vizicist/spacepalettepro/cad/SPP_hinge.3mf

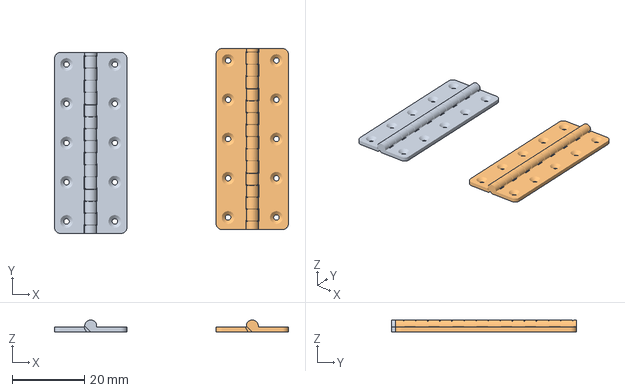
[picture p66: CAD file, 2025-05-30]
cad/SPP_hinge.3mf
64.6 x 51.1 x 3.33 mm
Print in place hinge FDM (x60y150).stl x 2
