vizicist/spacepalettepro/dxf/SPP_basebox_frontback.dxf

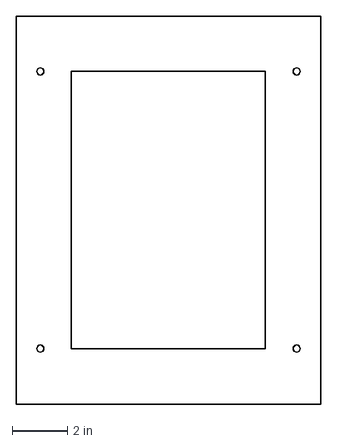
[picture p67: CAD file, 2022-07-03]
dxf/SPP_basebox_frontback.dxf
11.0 x 14.0 in
