vizicist/spacepalettepro/pre2025/dxf/SPP_baseboxes_medium_back_outer.dxf

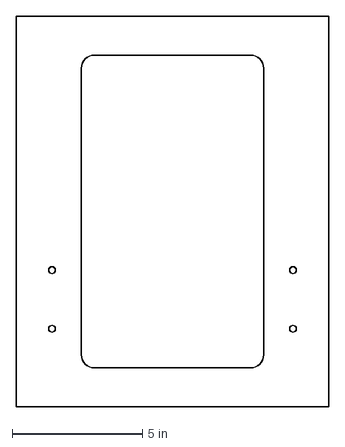
[picture p68: CAD file, 2022-09-05]
pre2025/dxf/SPP_baseboxes_medium_back_outer.dxf
12.0 x 15.0 in
