vizicist/spacepalettepro/pre2025/stl/AI3MX_amp_bracket_half.3mf

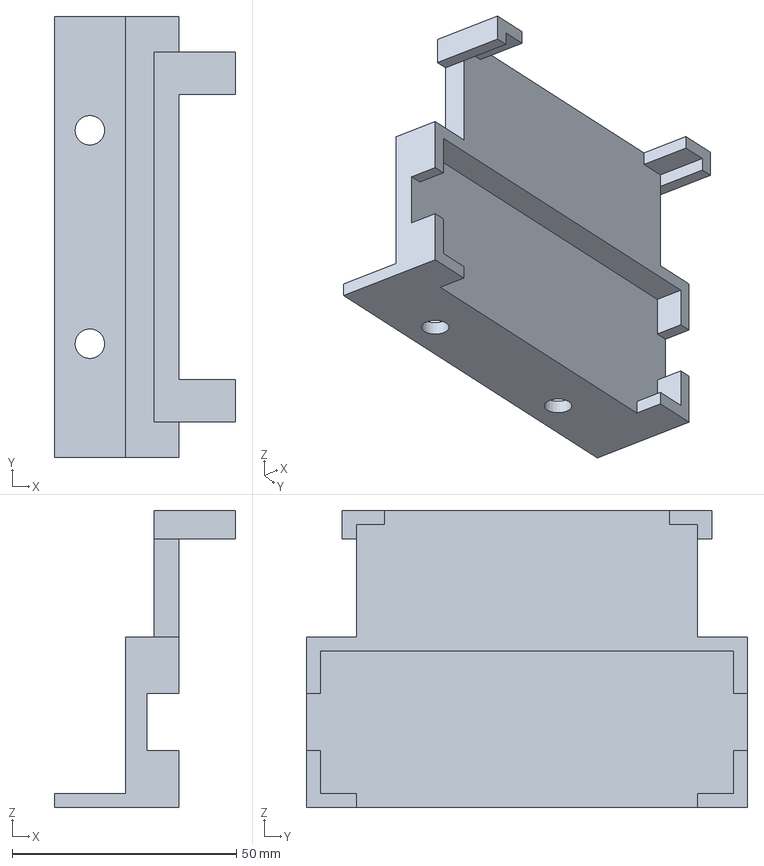
[picture p69: CAD file, 2021-08-21]
pre2025/stl/AI3MX_amp_bracket_half.3mf
40.5 x 98.4 x 66.3 mm
