vizicist/spacepalettepro/cad/SPP_angle.stl

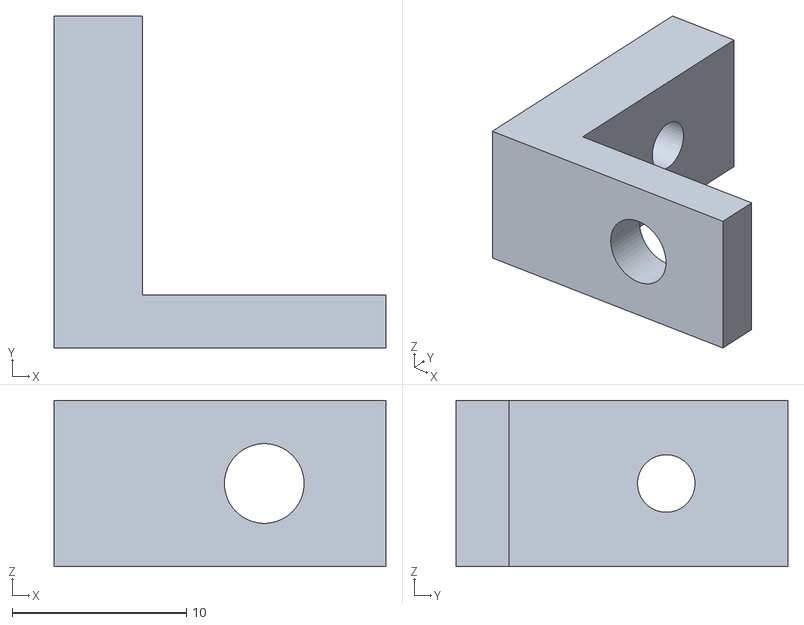
[picture p70: CAD file, 2025-05-30]
cad/SPP_angle.stl
19.0 x 19.0 x 9.53
