vizicist/spacepalettepro/pre2025/dxf/SPP_baseboxes_medium_back.dxf

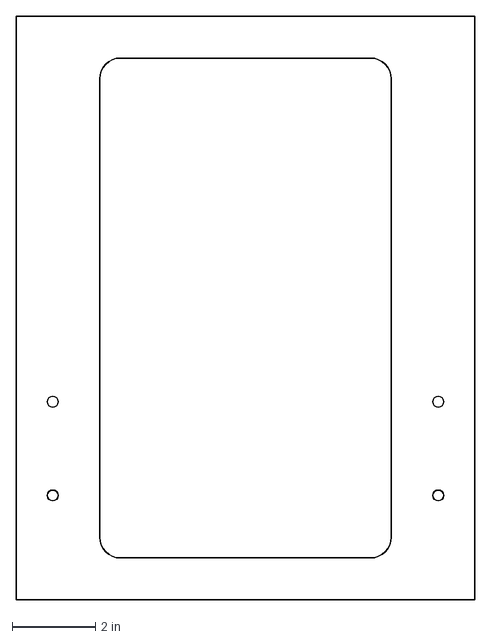
[picture p71: CAD file, 2022-09-05]
pre2025/dxf/SPP_baseboxes_medium_back.dxf
11.0 x 14.0 in
