vizicist/spacepalettepro/pre2025/stl/amp_bracket_half.stl

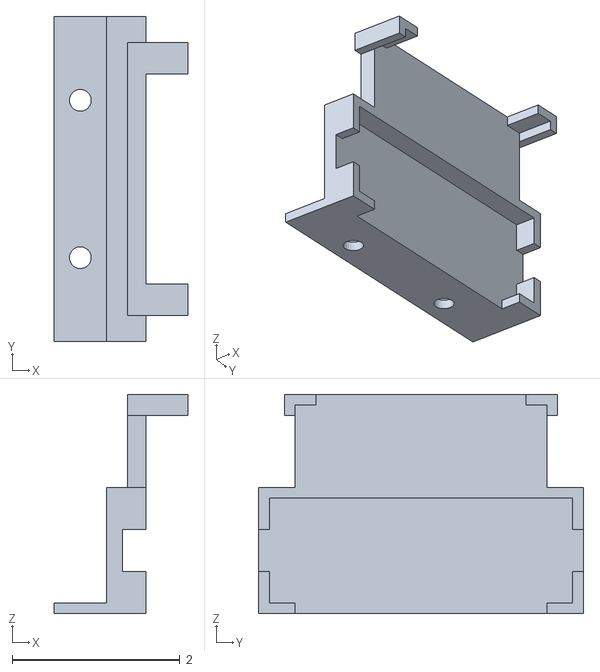
[picture p72: CAD file, 2021-08-21]
pre2025/stl/amp_bracket_half.stl
1.59 x 3.88 x 2.61
