vizicist/spacepalettepro/cad/SPP_ladder.3mf

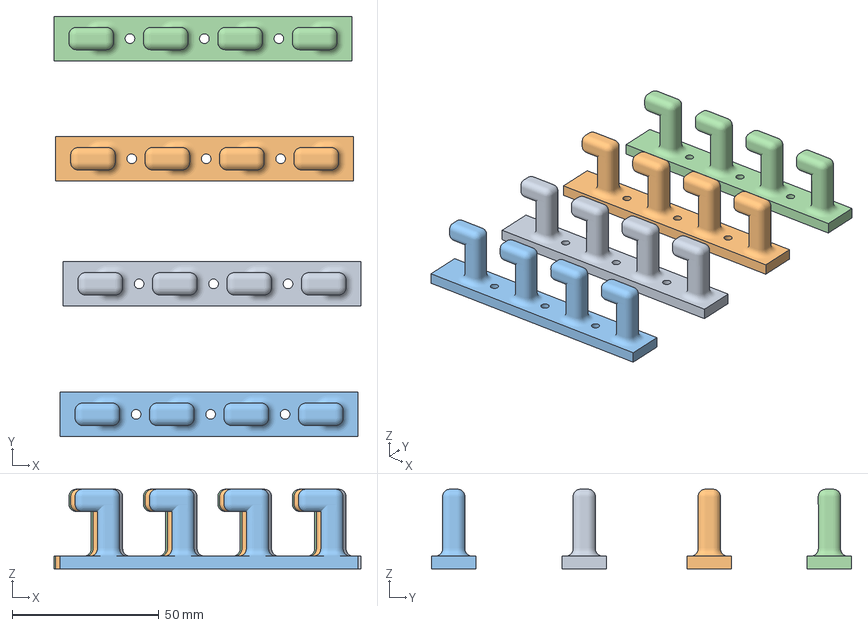
[picture p73: CAD file, 2025-05-30]
cad/SPP_ladder.3mf
104.7 x 143.4 x 27.2 mm
SPP_ladder.stl x 4
