vizicist/spacepalettepro/dxf/SPP_BaseHeadphones.dxf

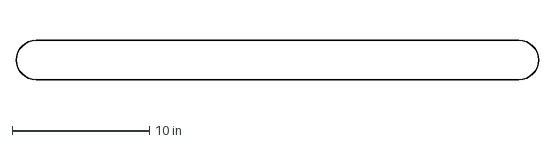
[picture p74: CAD file, 2021-08-06]
dxf/SPP_BaseHeadphones.dxf
38.0 x 2.88 in
