vizicist/spacepalettepro/pre2025/dxf/SPP_Layer7_back.dxf

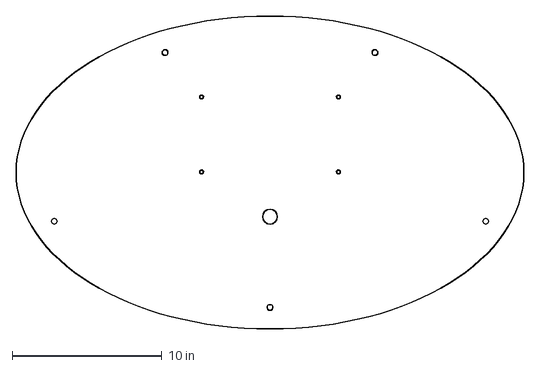
[picture p75: CAD file, 2022-08-22]
pre2025/dxf/SPP_Layer7_back.dxf
33.9 x 20.9 in
