vizicist/spacepalettepro/cad/SPP_sidesupport8.stl

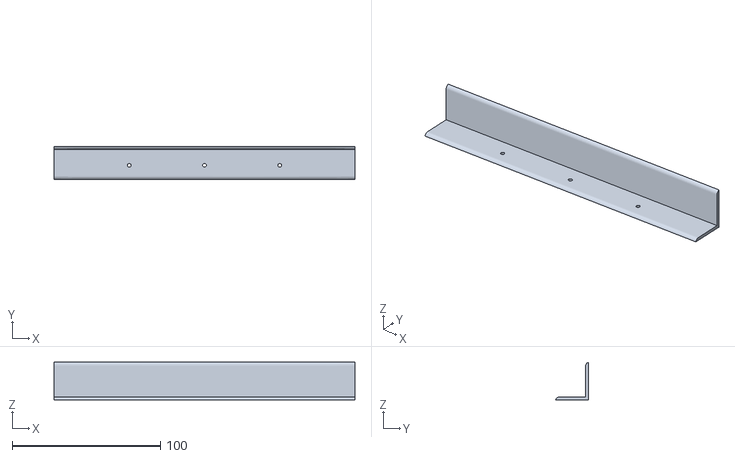
[picture p76: CAD file, 2025-05-30]
cad/SPP_sidesupport8.stl
203.2 x 22.2 x 25.4
