vizicist/spacepalettepro/pre2025/dxf/SPP_baseboxes_small_side.dxf

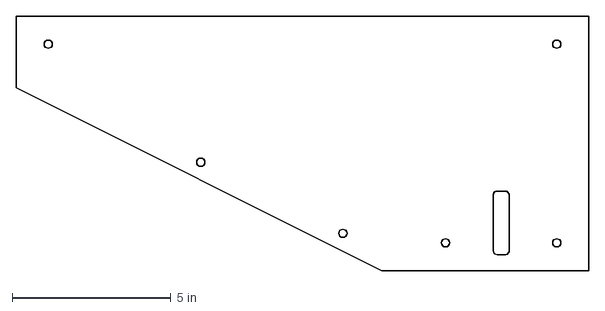
[picture p77: CAD file, 2022-08-22]
pre2025/dxf/SPP_baseboxes_small_side.dxf
18.0 x 8.00 in
