vizicist/spacepalettepro/pre2025/stl/amp_bracket.obj

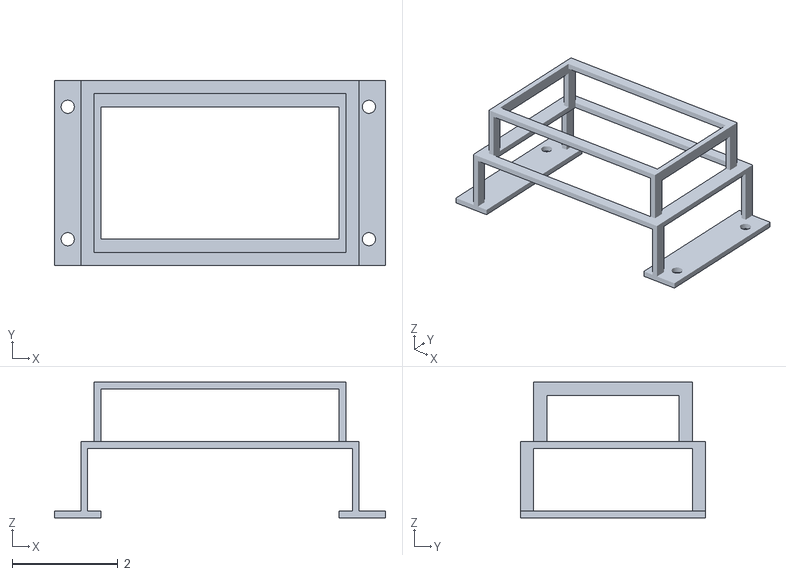
[picture p78: CAD file, 2021-08-17]
pre2025/stl/amp_bracket.obj
6.25 x 3.50 x 2.56
