vizicist/spacepalettepro/cad/SPP_ladder_4.3mf

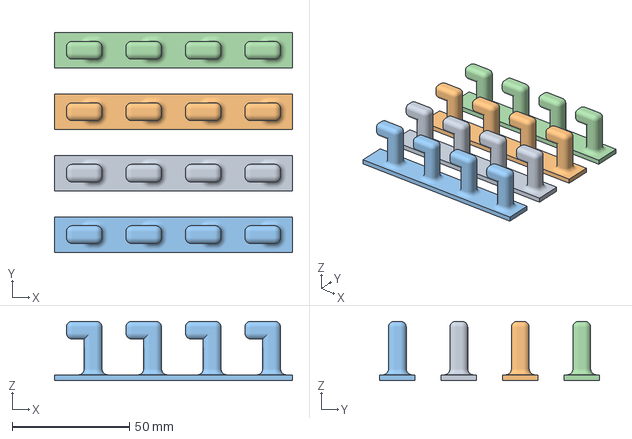
[picture p79: CAD file, 2025-05-30]
cad/SPP_ladder_4.3mf
101.6 x 94.0 x 25.4 mm
SPP_ladder.stl x 4
