vizicist/spacepalettepro/pre2025/dxf/SPP_baseboxes_small_back.dxf

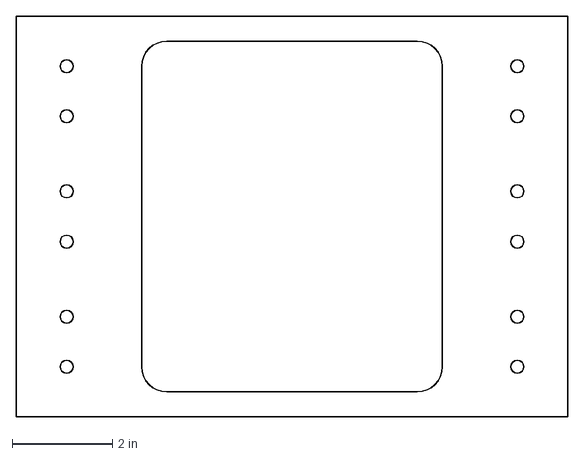
[picture p80: CAD file, 2022-08-15]
pre2025/dxf/SPP_baseboxes_small_back.dxf
11.0 x 8.00 in
