vizicist/spacepalettepro/pre2025/stl/corner_mount.stl

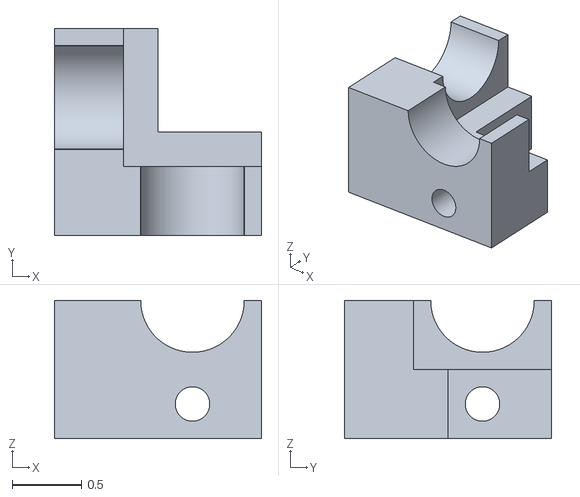
[picture p81: CAD file, 2021-08-06]
pre2025/stl/corner_mount.stl
1.50 x 1.50 x 1.00
