vizicist/spacepalettepro/cad/SPP_ladder_holes.3mf

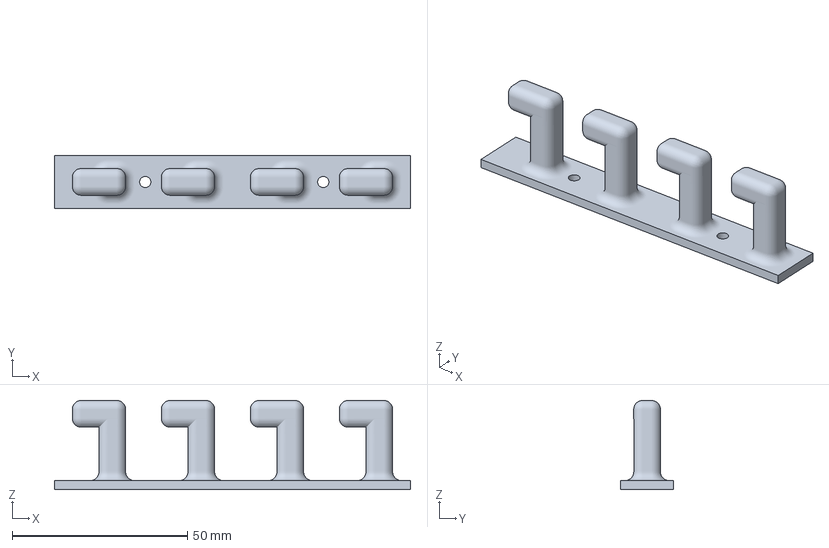
[picture p82: CAD file, 2025-05-30]
cad/SPP_ladder_holes.3mf
101.6 x 15.2 x 25.4 mm
