vizicist/spacepalettepro/pre2025/dxf/SPP_BaseBottom.dxf

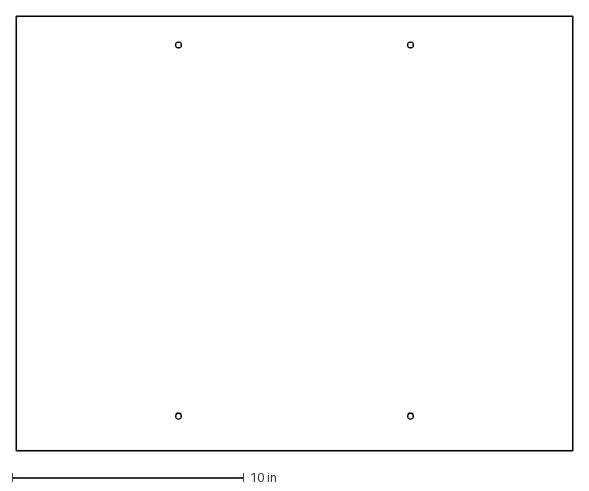
[picture p83: CAD file, 2022-08-15]
pre2025/dxf/SPP_BaseBottom.dxf
24.0 x 18.8 in
