vizicist/spacepalettepro/cad/SPP_portpanel_orig.3mf

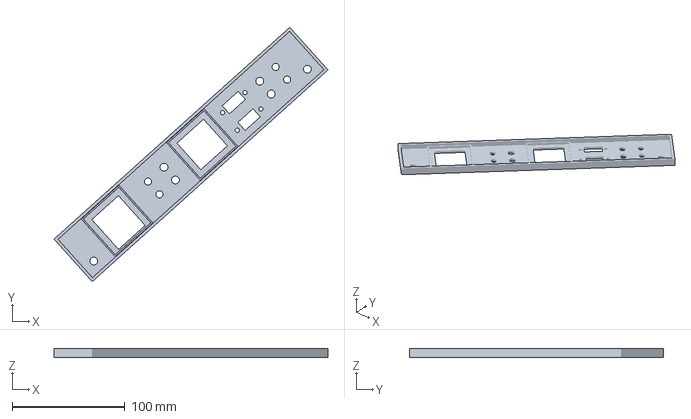
[picture p84: CAD file, 2025-05-30]
cad/SPP_portpanel_orig.3mf
243.3 x 225.8 x 7.62 mm
