vizicist/spacepalettepro/pre2025/dxf/SPP_BaseBottomLedge.dxf

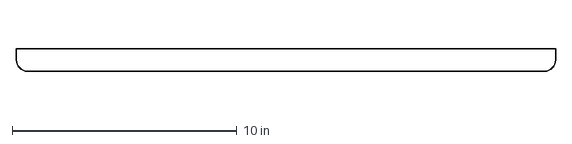
[picture p85: CAD file, 2022-08-15]
pre2025/dxf/SPP_BaseBottomLedge.dxf
24.0 x 1.00 in
