vizicist/spacepalettepro/cad/SPP_InnerEdge_B_0.25.stl

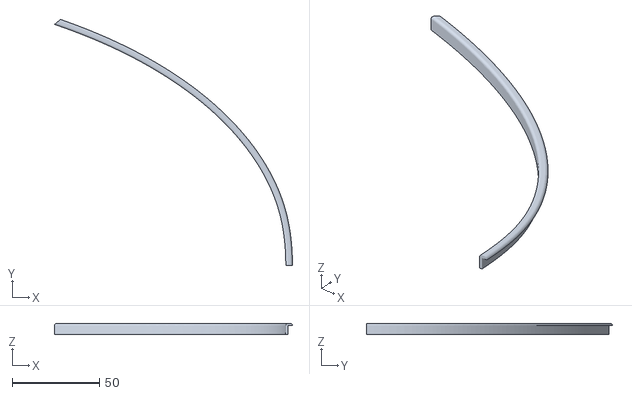
[picture p86: CAD file, 2025-05-30]
cad/SPP_InnerEdge_B_0.25.stl
136.2 x 140.9 x 6.35
