vizicist/spacepalettepro/pre2025/dxf/SPP_BaseSpeaker.dxf

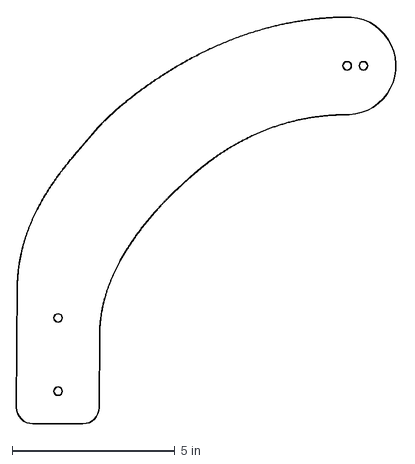
[picture p87: CAD file, 2022-07-30]
pre2025/dxf/SPP_BaseSpeaker.dxf
11.7 x 12.5 in
