vizicist/spacepalettepro/cad/SPP_Edge_All.3mf

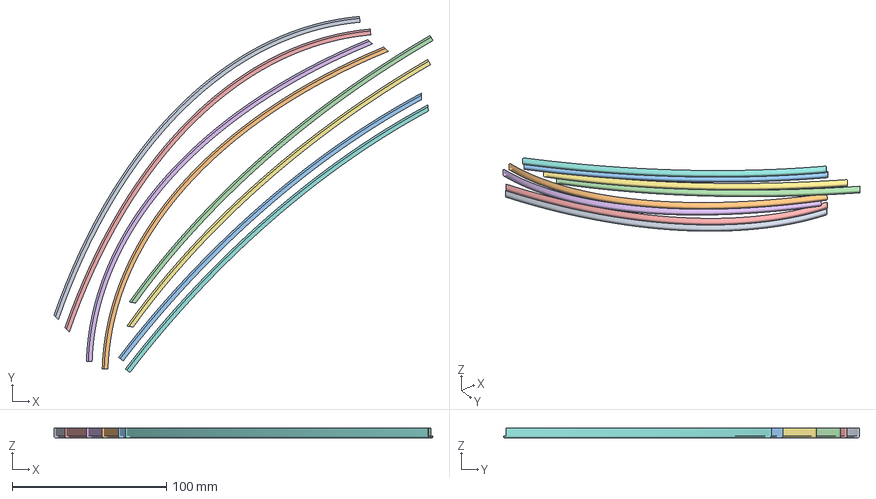
[picture p88: CAD file, 2025-05-30]
cad/SPP_Edge_All.3mf
246.1 x 231.2 x 6.35 mm
SPP_Edge_B_0.25.stl x 2
SPP_Edge_B_0.25_flipped.stl x 2
SPP_Edge_A_0.25.stl x 2
SPP_Edge_A_0.25_flipped.stl x 2
