vizicist/spacepalettepro/pre2025/dxf/SPP_BaseHeadphones_small.dxf

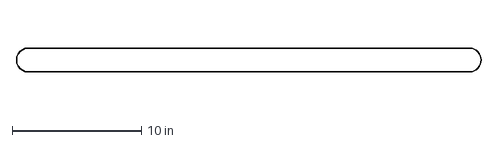
[picture p89: CAD file, 2022-07-30]
pre2025/dxf/SPP_BaseHeadphones_small.dxf
36.0 x 1.86 in
