vizicist/spacepalettepro/cad/SPP_hingetest.3mf

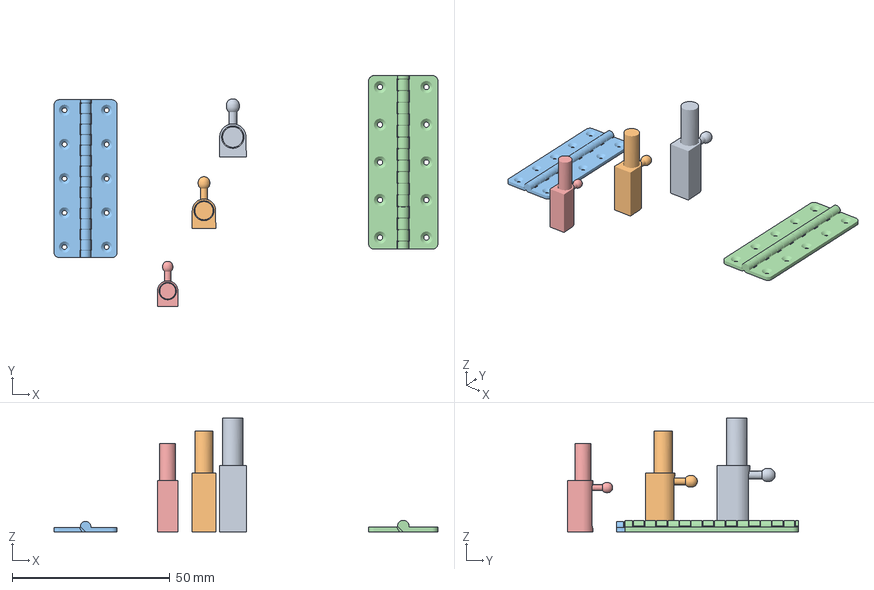
[picture p90: CAD file, 2025-05-30]
cad/SPP_hingetest.3mf
121.6 x 73.1 x 36.0 mm
SPP_slidercut.stl x 3
Print in place hinge FDM (x60y150).stl x 2
