vizicist/spacepalettepro/pre2025/dxf/SPP_BaseBack_insert.dxf

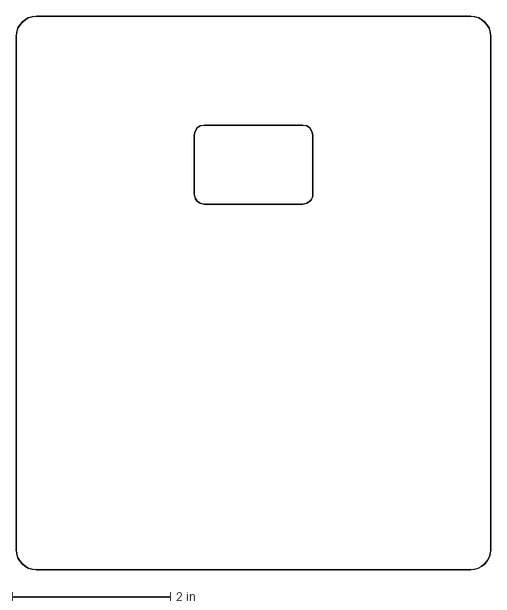
[picture p91: CAD file, 2022-07-30]
pre2025/dxf/SPP_BaseBack_insert.dxf
6.00 x 7.00 in
