vizicist/spacepalettepro/cad/SPP_headphonehook.3mf

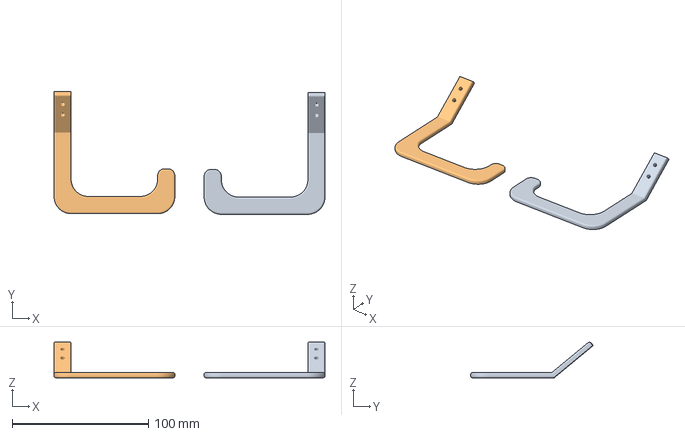
[picture p92: CAD file, 2025-05-30]
cad/SPP_headphonehook.3mf
199.0 x 90.1 x 26.1 mm
SPP_headphonehook.stl x 2
