vizicist/spacepalettepro/pre2025/dxf/SPP_baseboxes_large_back.dxf

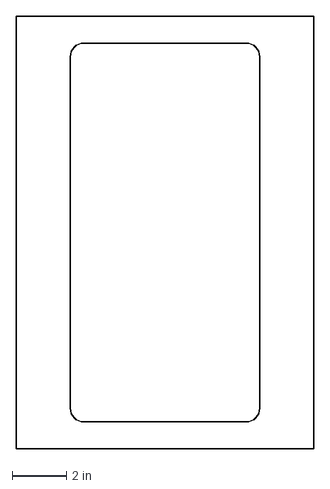
[picture p93: CAD file, 2022-07-30]
pre2025/dxf/SPP_baseboxes_large_back.dxf
11.0 x 16.0 in
