vizicist/spacepalettepro/cad/SPP_Edge_A_0.25.stl

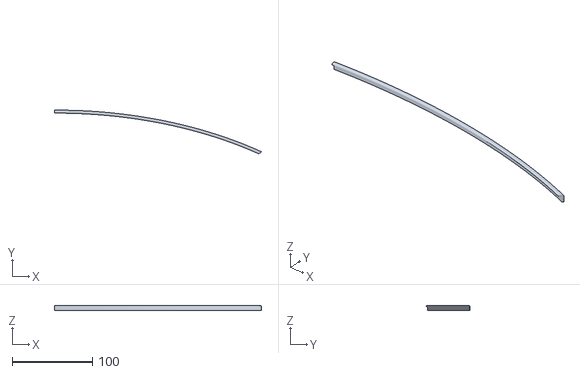
[picture p94: CAD file, 2025-05-30]
cad/SPP_Edge_A_0.25.stl
257.3 x 54.5 x 6.35
