vizicist/spacepalettepro/pre2025/dxf/SPP_baseboxes_small_top.dxf

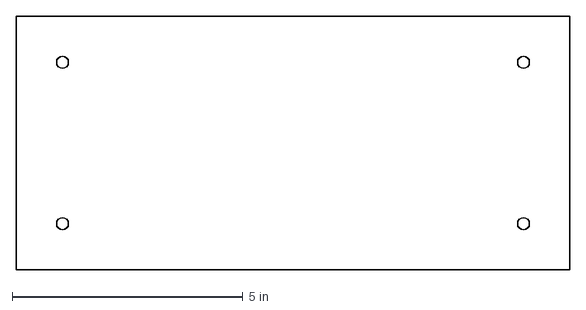
[picture p95: CAD file, 2022-07-30]
pre2025/dxf/SPP_baseboxes_small_top.dxf
12.0 x 5.50 in
