vizicist/spacepalettepro/cad/SPP_pinpanel.stl

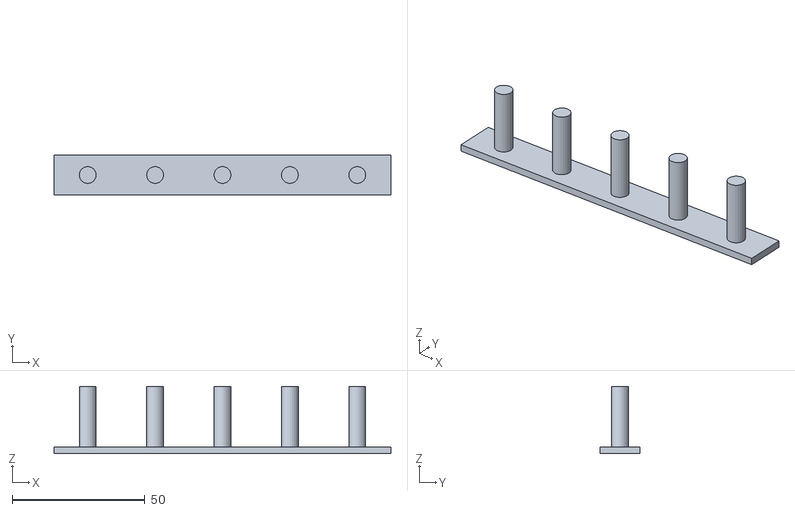
[picture p96: CAD file, 2025-05-30]
cad/SPP_pinpanel.stl
127.0 x 15.2 x 25.4
