vizicist/spacepalettepro/pre2025/dxf/SPP_BaseBack.dxf

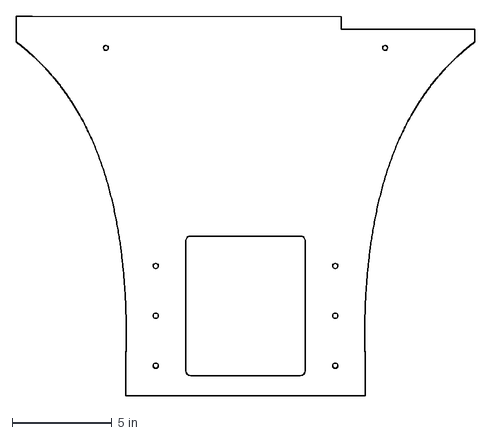
[picture p97: CAD file, 2022-07-30]
pre2025/dxf/SPP_BaseBack.dxf
23.0 x 19.0 in
