vizicist/spacepalettepro/cad/SPP_back.dxf

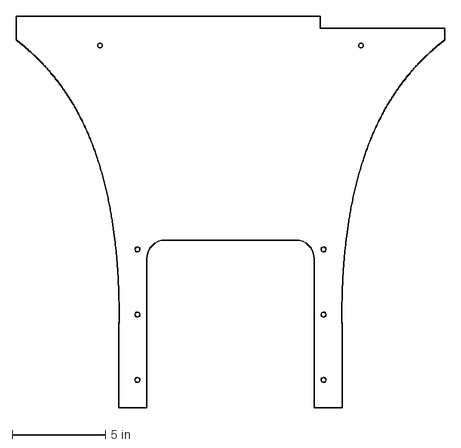
[picture p98: CAD file, 2025-05-30]
cad/SPP_back.dxf
23.0 x 21.0 in
