vizicist/spacepalettepro/pre2025/dxf/SPP_baseboxes_medium_side.dxf

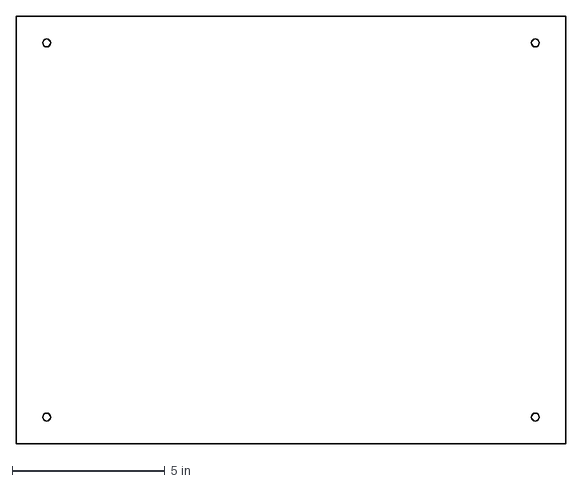
[picture p99: CAD file, 2022-07-30]
pre2025/dxf/SPP_baseboxes_medium_side.dxf
18.0 x 14.0 in
