vizicist/spacepalettepro/cad/SPP_headphonehookold.3mf

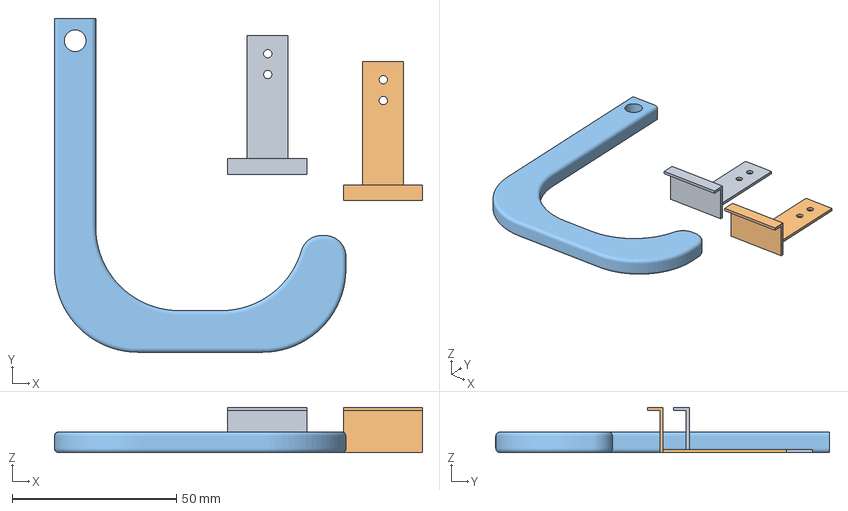
[picture p100: CAD file, 2025-05-30]
cad/SPP_headphonehookold.3mf
112.1 x 101.6 x 13.8 mm
SPP_latch.stl x 2
SPP_headphonehook.stl
