vizicist/spacepalettepro/pre2025/dxf/SPP_baseboxes_large_side.dxf

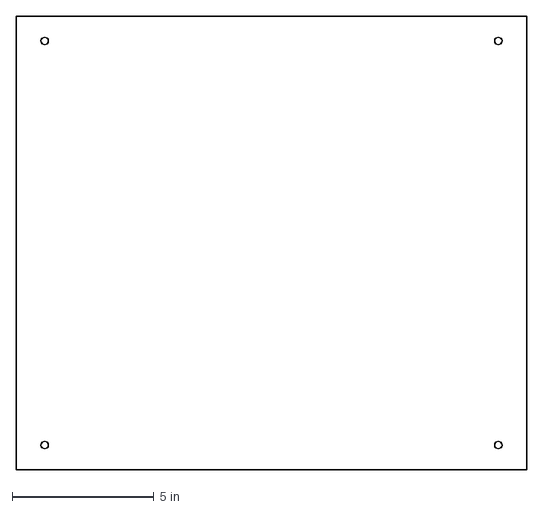
[picture p101: CAD file, 2022-07-14]
pre2025/dxf/SPP_baseboxes_large_side.dxf
18.0 x 16.0 in
