vizicist/spacepalettepro/cad/SPP_slider.3mf

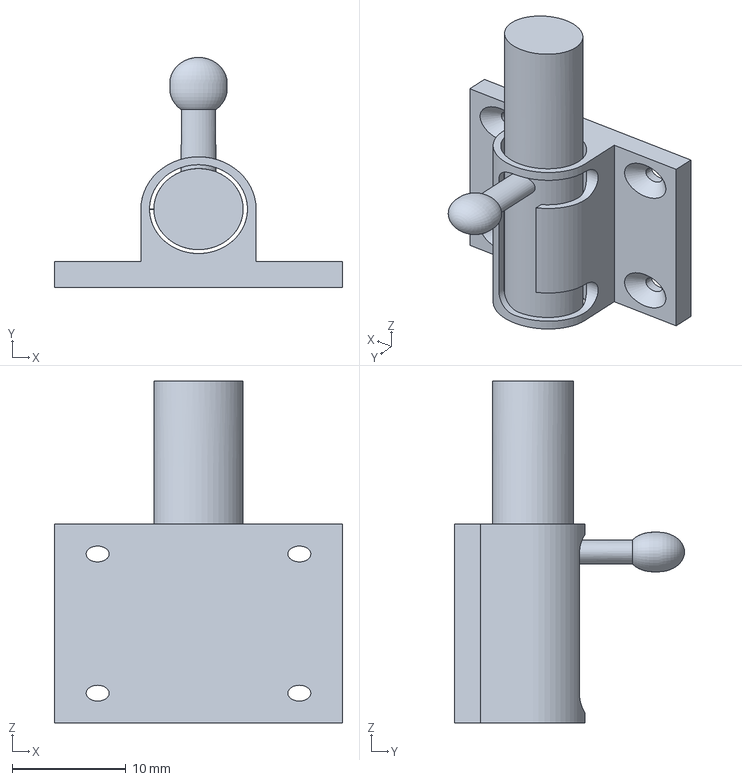
[picture p102: CAD file, 2025-05-30]
cad/SPP_slider.3mf
25.3 x 20.2 x 30.0 mm
