vizicist/spacepalettepro/pre2025/dxf/SPP_BaseFront.dxf

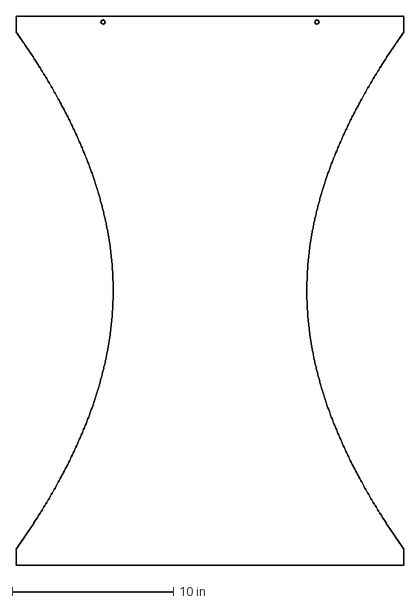
[picture p103: CAD file, 2022-01-15]
pre2025/dxf/SPP_BaseFront.dxf
24.0 x 34.0 in
