vizicist/spacepalettepro/cad/SPP_channels_hooks.3mf

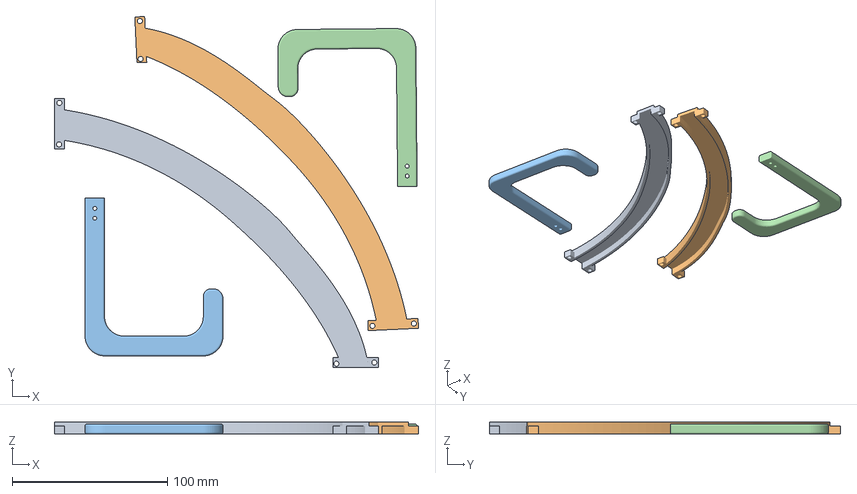
[picture p104: CAD file, 2025-05-30]
cad/SPP_channels_hooks.3mf
234.1 x 225.8 x 7.62 mm
SPP_wirechannel.stl_1
SPP_wirechannel.stl_2
SPP_headphonehook.stl x 2
