vizicist/spacepalettepro/pre2025/dxf/SPP_MonLayer5.dxf

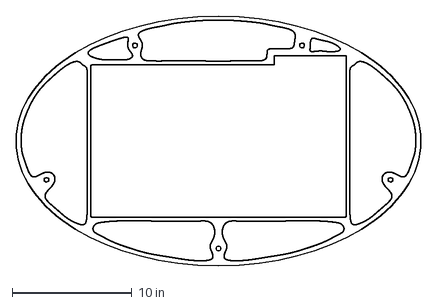
[picture p105: CAD file, 2022-01-15]
pre2025/dxf/SPP_MonLayer5.dxf
33.9 x 20.9 in
