vizicist/spacepalettepro/cad/SPP_test.stl

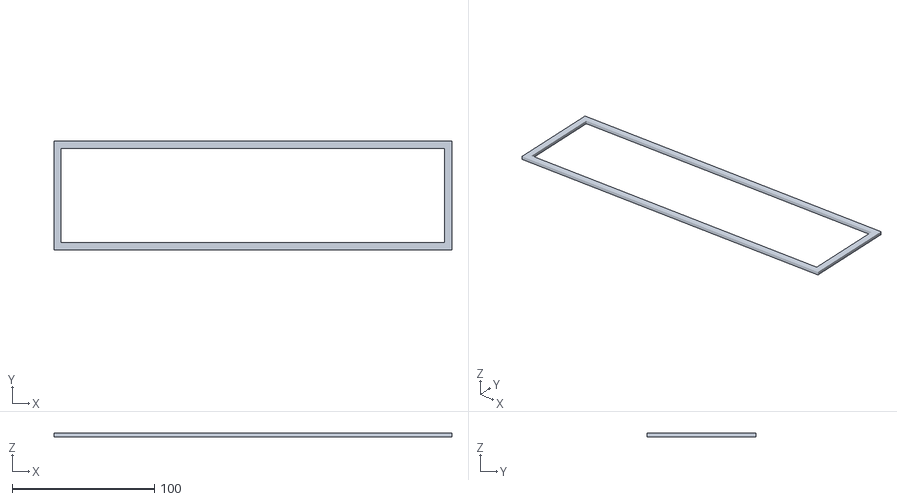
[picture p106: CAD file, 2025-05-30]
cad/SPP_test.stl
279.4 x 76.2 x 2.54
