vizicist/spacepalettepro/pre2025/dxf/SPP_MonLayer6_back.dxf

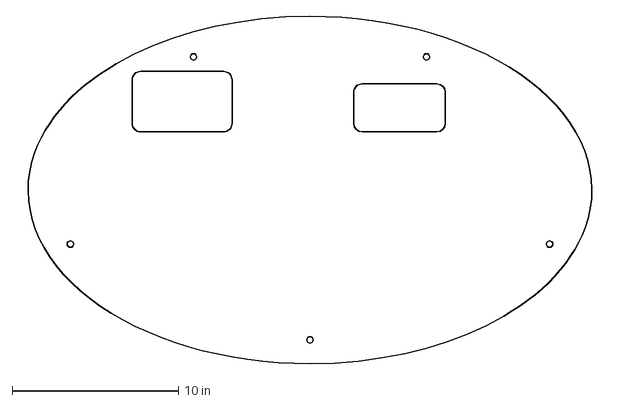
[picture p107: CAD file, 2022-01-15]
pre2025/dxf/SPP_MonLayer6_back.dxf
35.3 x 20.9 in
