vizicist/spacepalettepro/cad/SPP_fanpanel.dxf

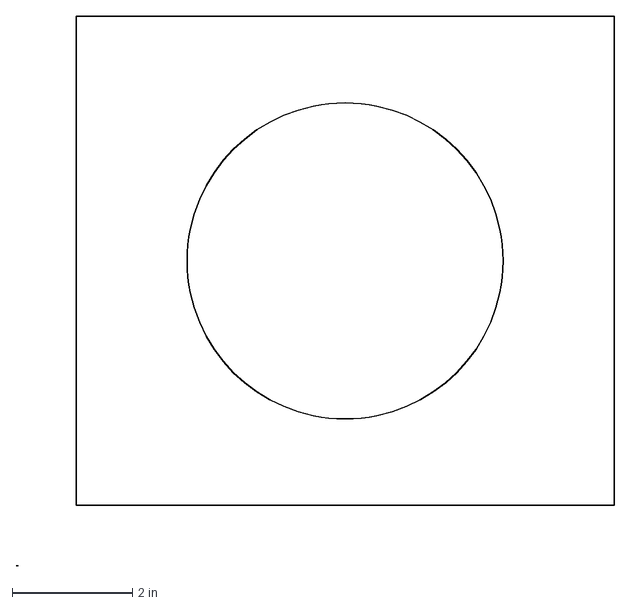
[picture p108: CAD file, 2025-05-30]
cad/SPP_fanpanel.dxf
9.94 x 9.13 in
