vizicist/spacepalettepro/pre2025/dxf/SPP_BaseBackBottom.dxf

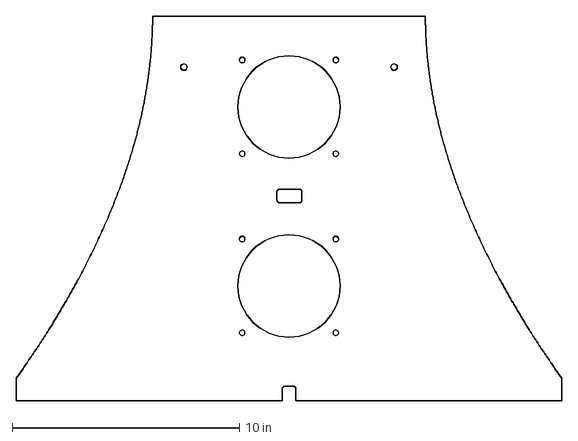
[picture p109: CAD file, 2021-08-20]
pre2025/dxf/SPP_BaseBackBottom.dxf
24.0 x 16.9 in
