vizicist/spacepalettepro/cad/SPP_mon_key_platform.3mf

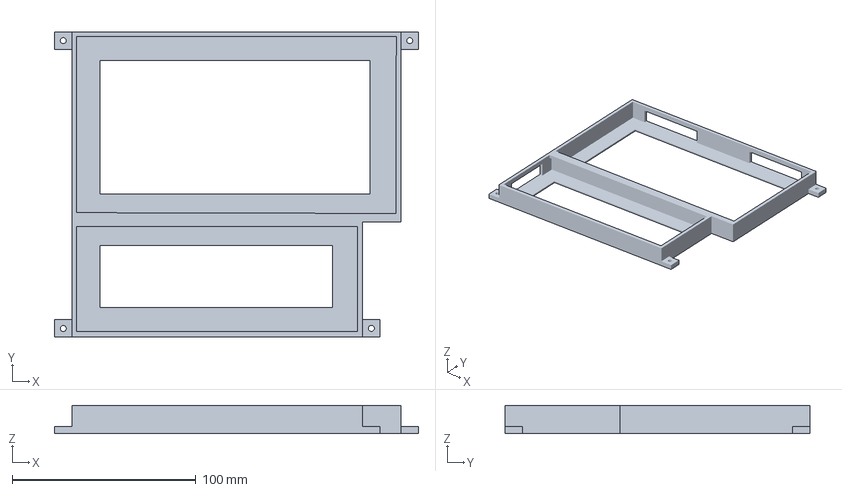
[picture p110: CAD file, 2025-05-30]
cad/SPP_mon_key_platform.3mf
197.9 x 166.0 x 15.2 mm
