vizicist/spacepalettepro/pre2025/dxf/SPP_MonLayer1_face.dxf

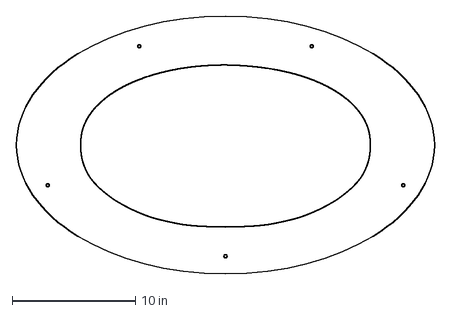
[picture p111: CAD file, 2021-08-10]
pre2025/dxf/SPP_MonLayer1_face.dxf
33.9 x 20.9 in
