vizicist/spacepalettepro/pre2025/dxf/SPP_BaseKeyboard.dxf

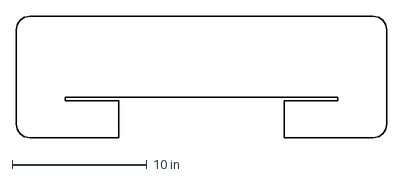
[picture p112: CAD file, 2021-08-06]
pre2025/dxf/SPP_BaseKeyboard.dxf
27.5 x 9.00 in
