vizicist/spacepalettepro/cad/SPP_back_insert.dxf

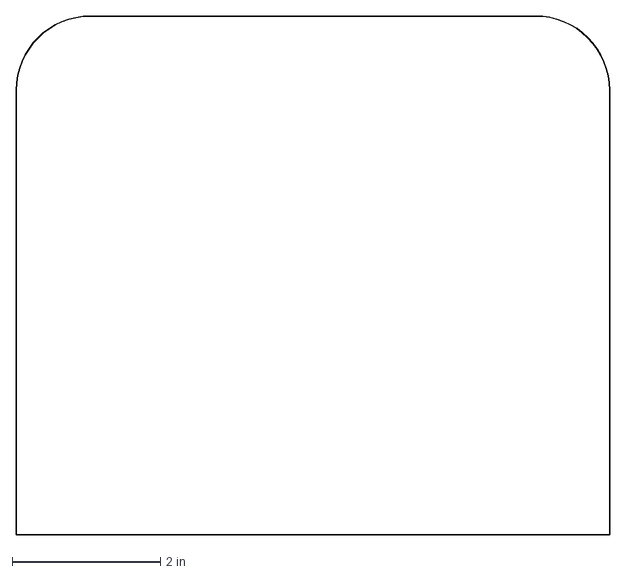
[picture p113: CAD file, 2025-05-30]
cad/SPP_back_insert.dxf
8.00 x 7.00 in
