vizicist/spacepalettepro/pre2025/dxf/SPP_Layer2.dxf

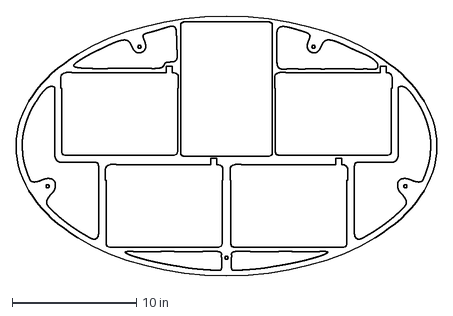
[picture p114: CAD file, 2021-08-06]
pre2025/dxf/SPP_Layer2.dxf
33.9 x 20.9 in
