vizicist/spacepalettepro/cad/SPP_Edge_A_all.3mf

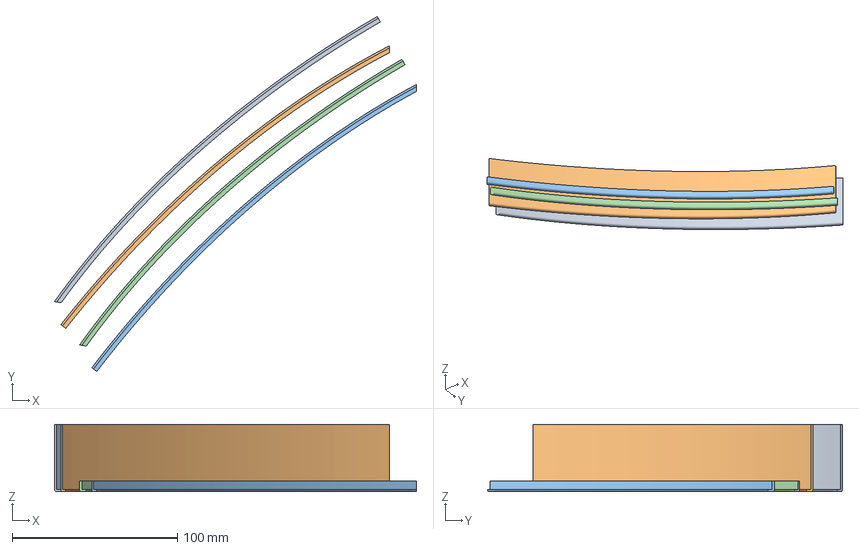
[picture p115: CAD file, 2025-05-30]
cad/SPP_Edge_A_all.3mf
219.4 x 215.1 x 40.8 mm
SPP_Edge_A_1.5_flipped.stl
SPP_Edge_A_1.5.stl
SPP_Edge_A_0.25.stl
SPP_Edge_A_0.25_flipped.stl
