vizicist/spacepalettepro/cad/SPP_pinangled.stl

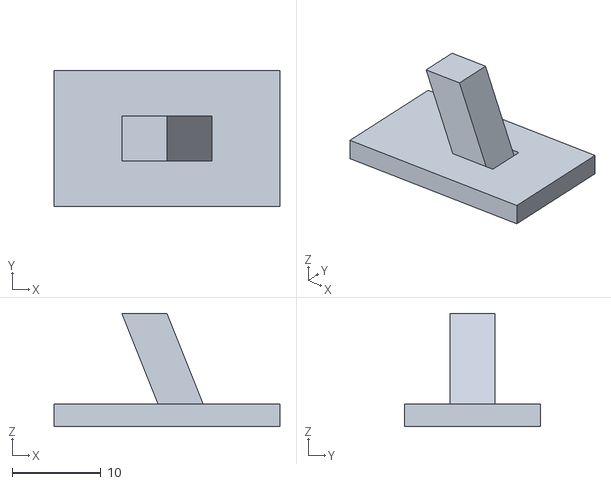
[picture p117: CAD file, 2025-05-30]
cad/SPP_pinangled.stl
25.4 x 15.2 x 12.7
