vizicist/spacepalettepro/pre2025/dxf/SPP_MonLayer2_3_bottom.dxf

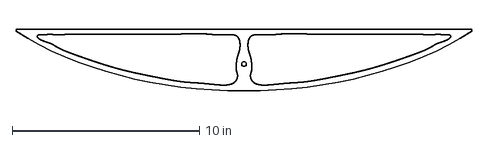
[picture p118: CAD file, 2021-08-06]
pre2025/dxf/SPP_MonLayer2_3_bottom.dxf
24.4 x 3.31 in
