vizicist/spacepalettepro/cad/SPP_switchcover.stl

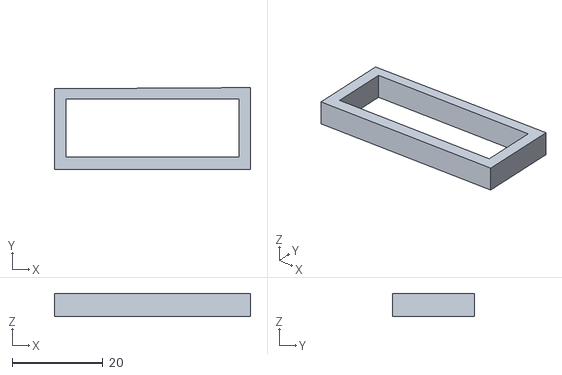
[picture p119: CAD file, 2025-05-30]
cad/SPP_switchcover.stl
43.2 x 18.0 x 5.08
