vizicist/spacepalettepro/pre2025/dxf/SPP_MonLayer4.dxf

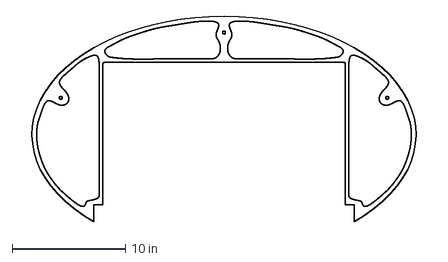
[picture p120: CAD file, 2021-08-06]
pre2025/dxf/SPP_MonLayer4.dxf
36.6 x 18.1 in
