vizicist/spacepalettepro/cad/SPP_basefrontb.dxf

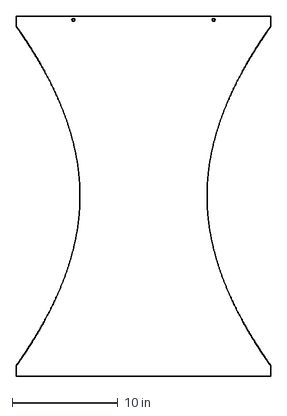
[picture p121: CAD file, 2025-05-30]
cad/SPP_basefrontb.dxf
24.0 x 34.0 in
