vizicist/spacepalettepro/pre2025/dxf/SPP_Layer3.dxf

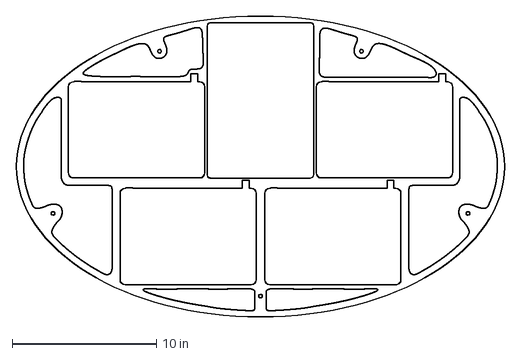
[picture p122: CAD file, 2021-08-06]
pre2025/dxf/SPP_Layer3.dxf
33.9 x 20.9 in
