vizicist/spacepalettepro/cad/SPP_Speaker.dxf

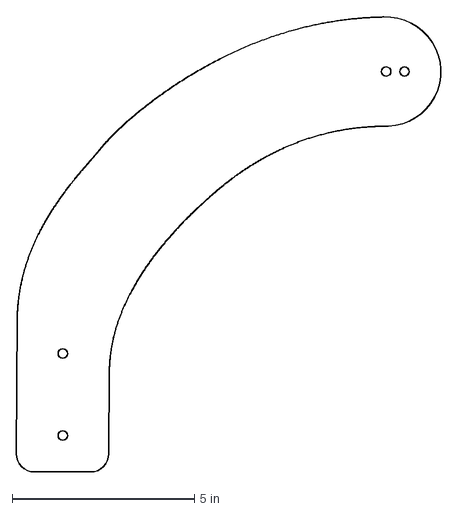
[picture p123: CAD file, 2025-05-30]
cad/SPP_Speaker.dxf
11.7 x 12.5 in
