vizicist/spacepalettepro/pre2025/dxf/SPP_MonLayer2_3_leftright.dxf

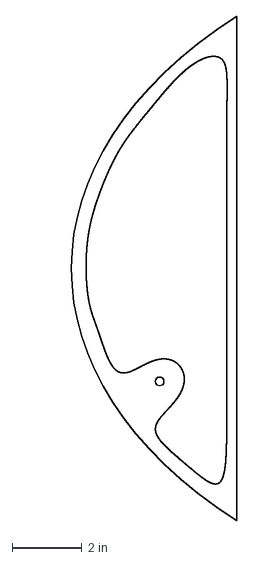
[picture p124: CAD file, 2021-08-06]
pre2025/dxf/SPP_MonLayer2_3_leftright.dxf
6.34 x 14.5 in
