vizicist/spacepalettepro/cad/SPP_wirechannel.stl

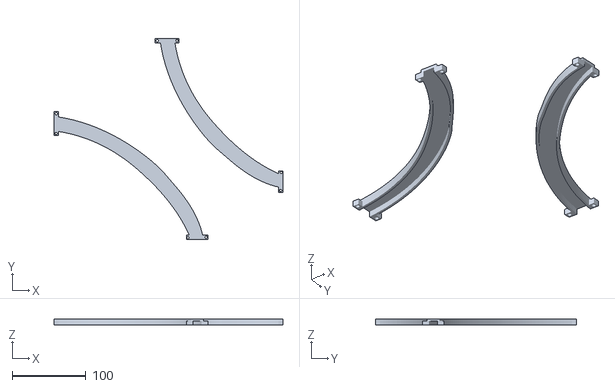
[picture p125: CAD file, 2025-05-30]
cad/SPP_wirechannel.stl
309.8 x 272.0 x 7.62
