vizicist/spacepalettepro/cad/SPP_nuc_support.3mf

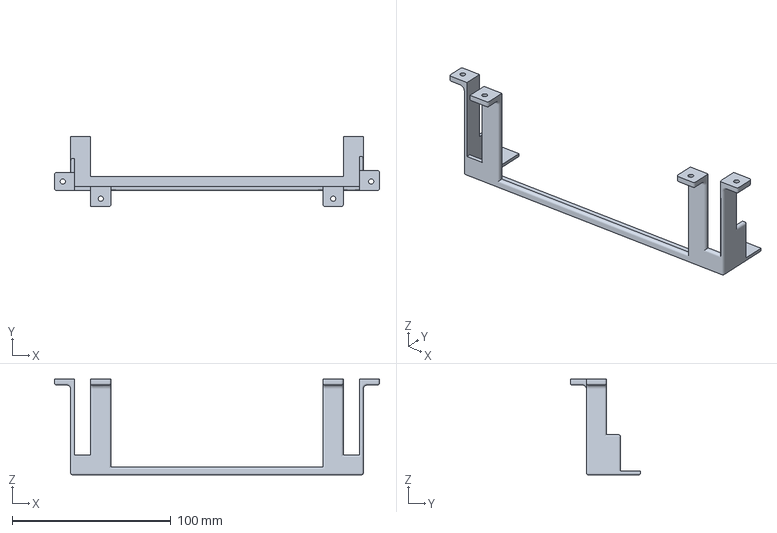
[picture p127: CAD file, 2025-05-30]
cad/SPP_nuc_support.3mf
205.0 x 44.4 x 60.5 mm
