vizicist/spacepalettepro/cad/SPP_latch.3mf

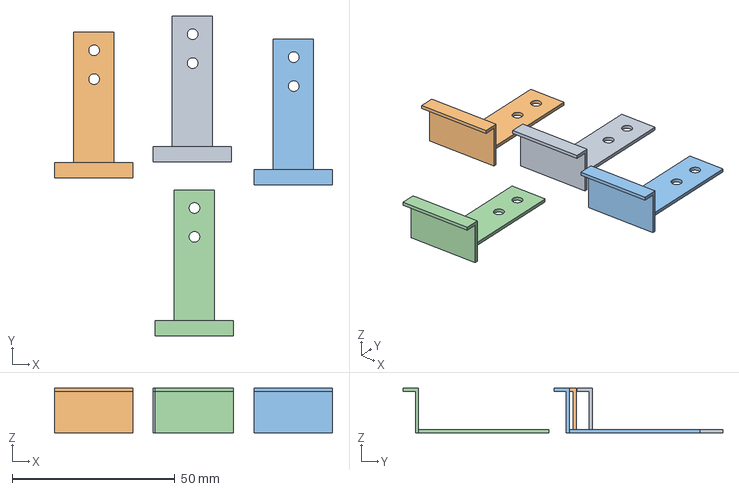
[picture p129: CAD file, 2025-05-30]
cad/SPP_latch.3mf
85.5 x 98.4 x 13.8 mm
SPP_latch.stl x 4
