vizicist/spacepalettepro/pre2025/dxf/SPP_MonLayer1orig_face.dxf

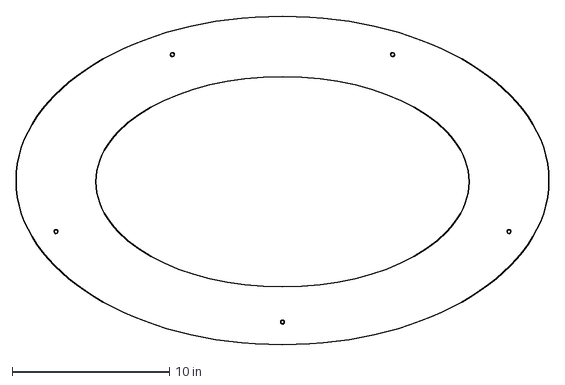
[picture p130: CAD file, 2021-08-06]
pre2025/dxf/SPP_MonLayer1orig_face.dxf
33.9 x 20.9 in
