vizicist/spacepalettepro/cad/SPP_usbholder.3mf

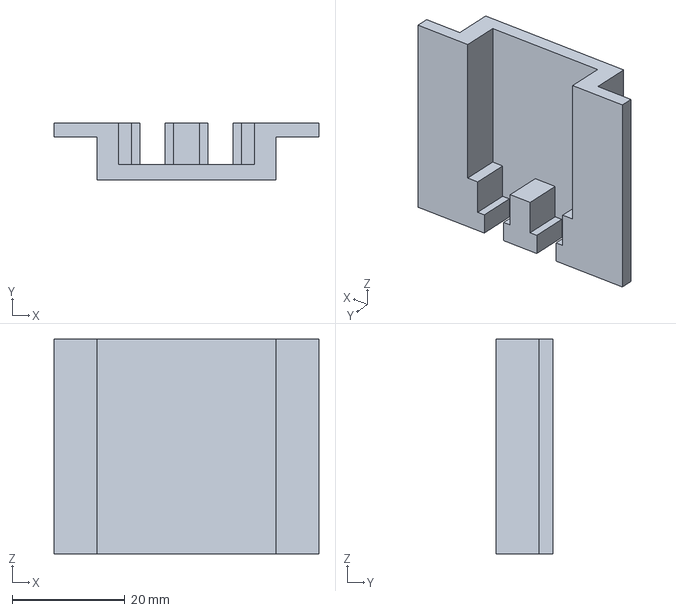
[picture p131: CAD file, 2025-05-30]
cad/SPP_usbholder.3mf
47.0 x 10.2 x 38.1 mm
