vizicist/spacepalettepro/pre2025/dxf/SPP_BaseMonKeyShelf.dxf

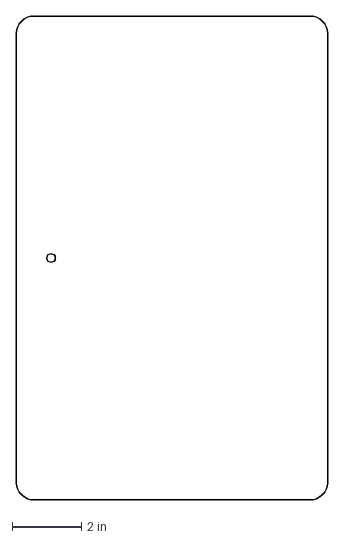
[picture p133: CAD file, 2021-08-06]
pre2025/dxf/SPP_BaseMonKeyShelf.dxf
9.00 x 14.0 in
