vizicist/spacepalettepro/cad/SPP_portpanel.3mf

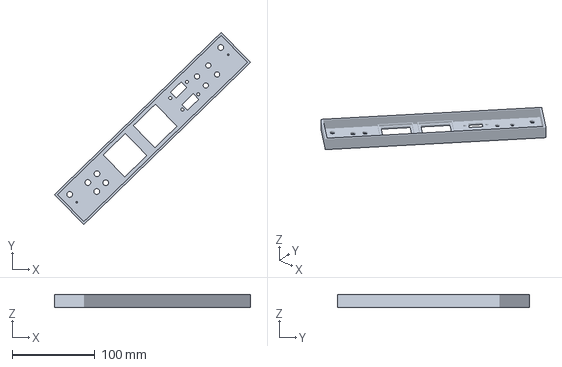
[picture p134: CAD file, 2025-05-30]
cad/SPP_portpanel.3mf
237.2 x 232.6 x 15.2 mm
