vizicist/spacepalettepro/pre2025/dxf/SPP_Layer5.dxf

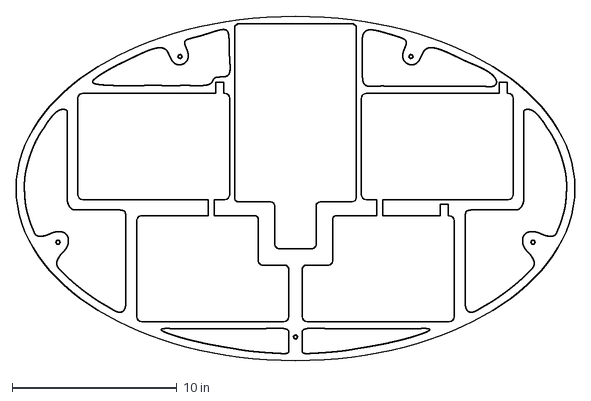
[picture p135: CAD file, 2021-08-06]
pre2025/dxf/SPP_Layer5.dxf
33.9 x 20.9 in
