vizicist/spacepalettepro/cad/SPP_monkeycables.3mf

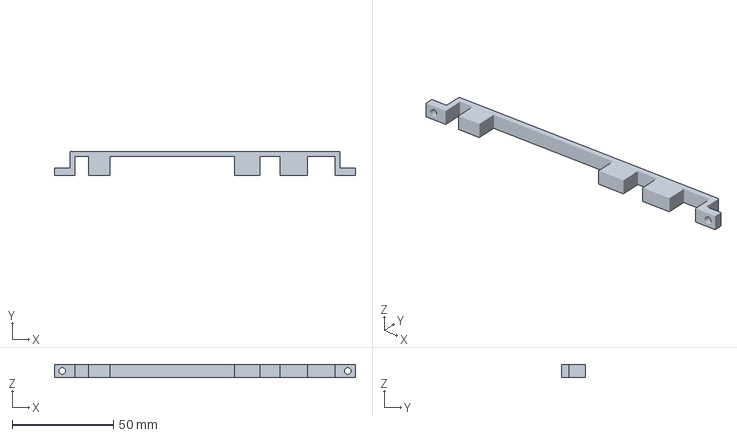
[picture p136: CAD file, 2025-05-30]
cad/SPP_monkeycables.3mf
148.8 x 12.1 x 6.35 mm
