vizicist/spacepalettepro/cad/SPP_headphonehookB.3mf

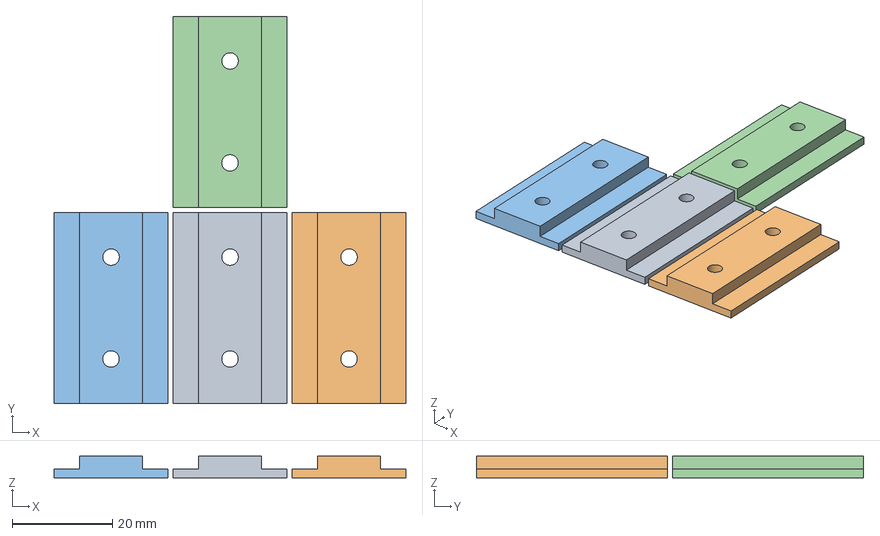
[picture p137: CAD file, 2025-05-30]
cad/SPP_headphonehookB.3mf
70.2 x 77.2 x 4.32 mm
SPP_headphonehookB.stl x 4
