vizicist/spacepalettepro/cad/SPP_Edge_B_all.3mf

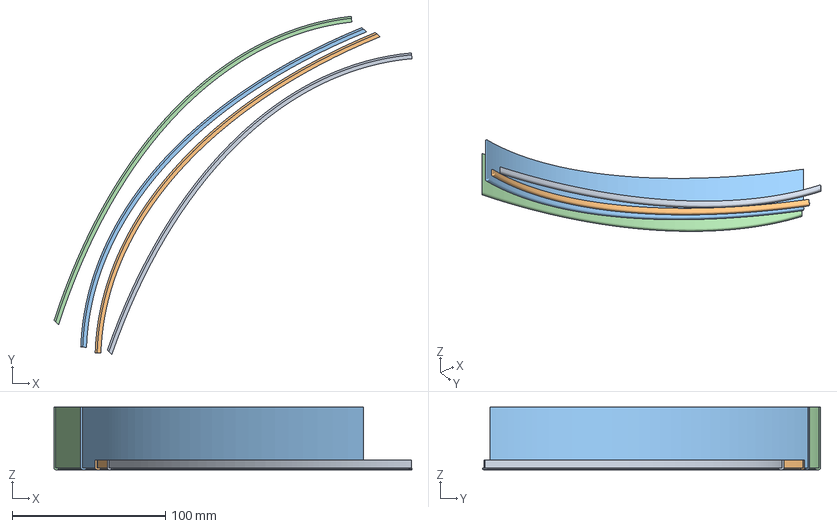
[picture p138: CAD file, 2025-05-30]
cad/SPP_Edge_B_all.3mf
233.4 x 220.7 x 40.8 mm
SPP_Edge_B_0.25.stl
SPP_Edge_B_0.25_flipped.stl
SPP_Edge_B_1.5_flipped.stl
SPP_Edge_B_1.5.stl
