vizicist/spacepalettepro/cad/SPP_Edge_A_0.25_flipped.3mf

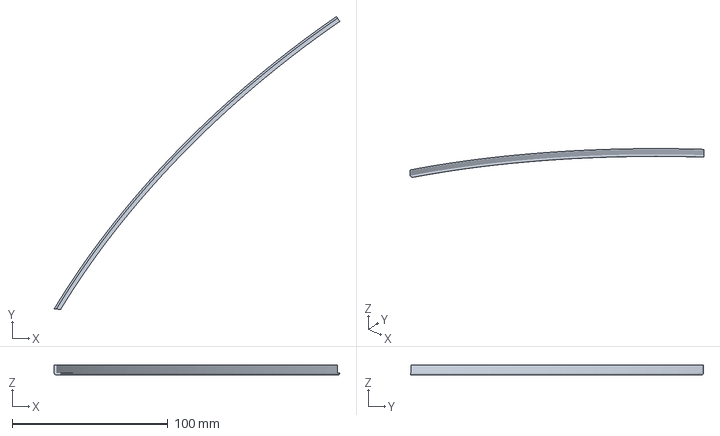
[picture p139: CAD file, 2025-05-30]
cad/SPP_Edge_A_0.25_flipped.3mf
183.4 x 188.1 x 6.35 mm
