vizicist/spacepalettepro/cad/SPP_touchscreen_outline.3mf

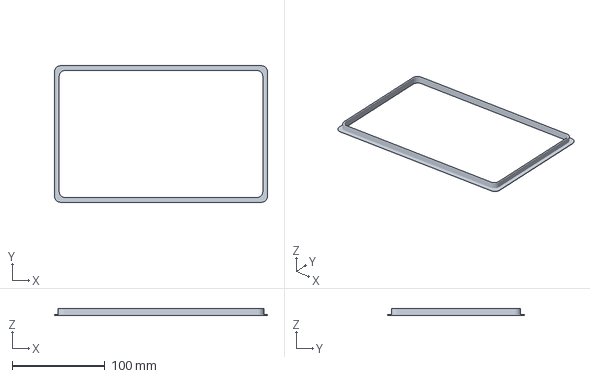
[picture p140: CAD file, 2025-05-30]
cad/SPP_touchscreen_outline.3mf
229.3 x 147.0 x 7.62 mm
