vizicist/spacepalettepro/cad/SPP_insert.dxf

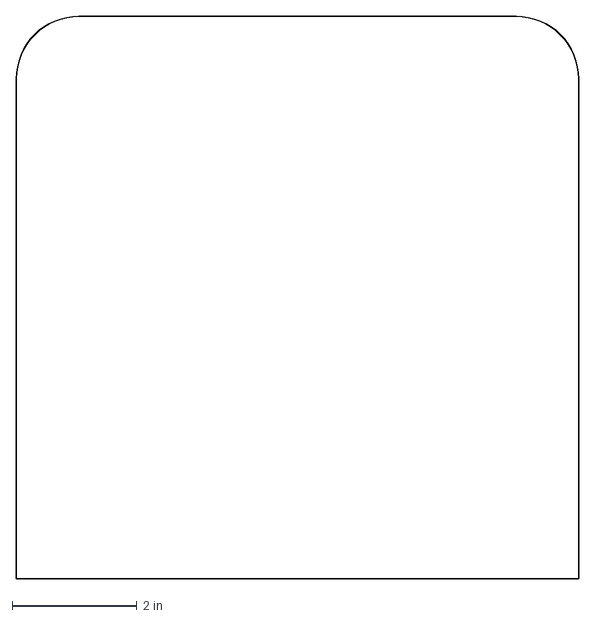
[picture p141: CAD file, 2025-05-30]
cad/SPP_insert.dxf
9.00 x 9.00 in
