vizicist/spacepalettepro/cad/SPP_angles.3mf

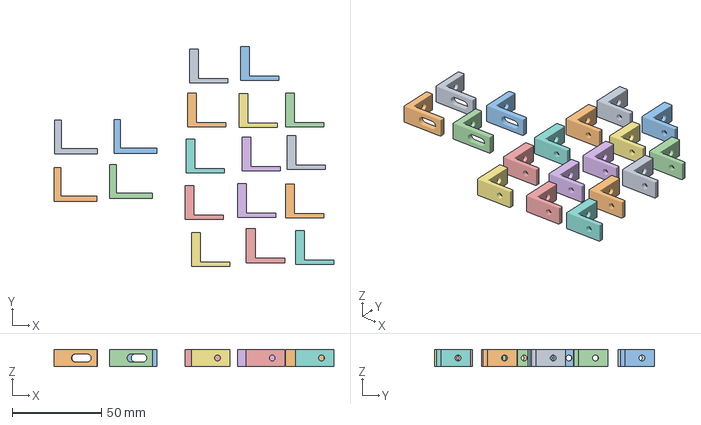
[picture p142: CAD file, 2025-05-30]
cad/SPP_angles.3mf
156.7 x 123.2 x 9.53 mm
SPP_angle4shelf.stl x 4
SPP_angle4front.stl x 14
