vizicist/spacepalettepro/cad/SPP_angle4shelf.3mf

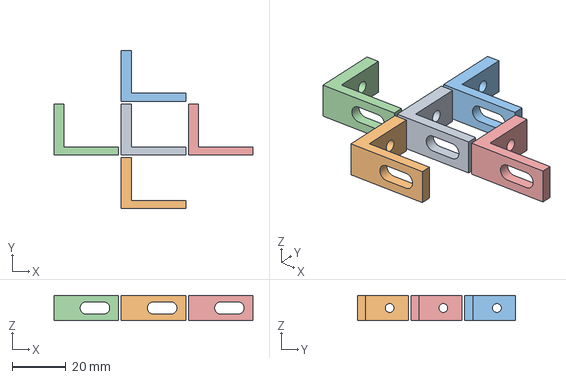
[picture p143: CAD file, 2025-05-30]
cad/SPP_angle4shelf.3mf
74.4 x 59.2 x 9.53 mm
SPP_angle4shelf.stl x 5
