vizicist/spacepalettepro/cad/SPP_Edge_B_0.25.stl

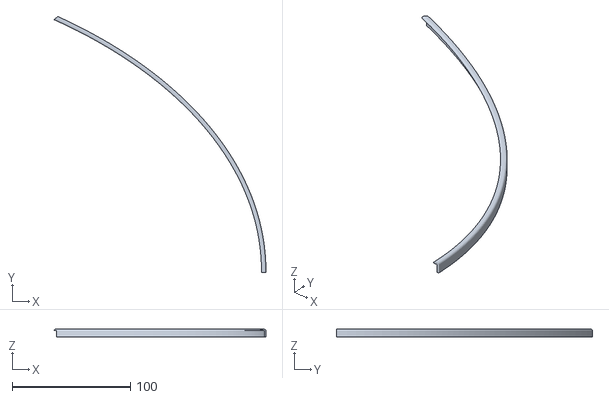
[picture p144: CAD file, 2025-05-30]
cad/SPP_Edge_B_0.25.stl
178.9 x 216.2 x 6.35
