vizicist/spacepalettepro/cad/SPP_headphone_support.3mf

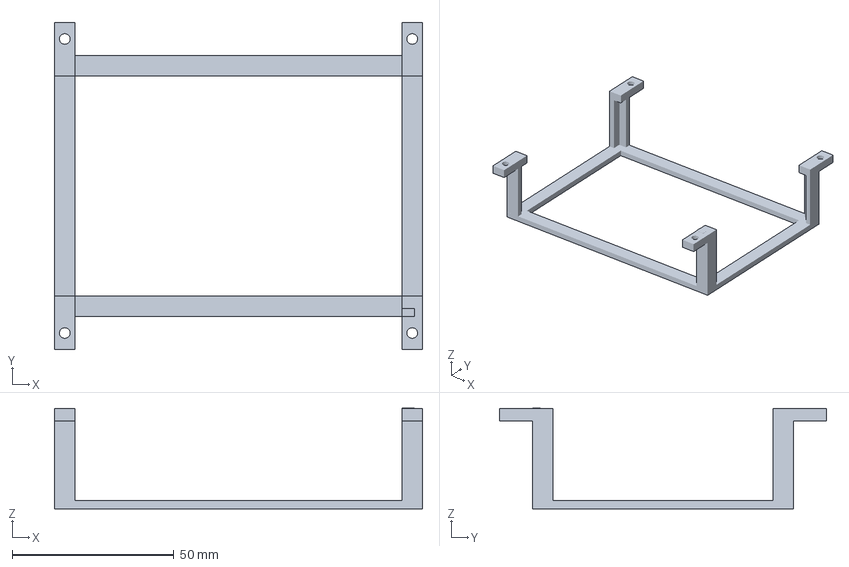
[picture p145: CAD file, 2025-05-30]
cad/SPP_headphone_support.3mf
113.8 x 101.1 x 31.1 mm
