vizicist/spacepalettepro/cad/SPP_InnerEdge_All.3mf

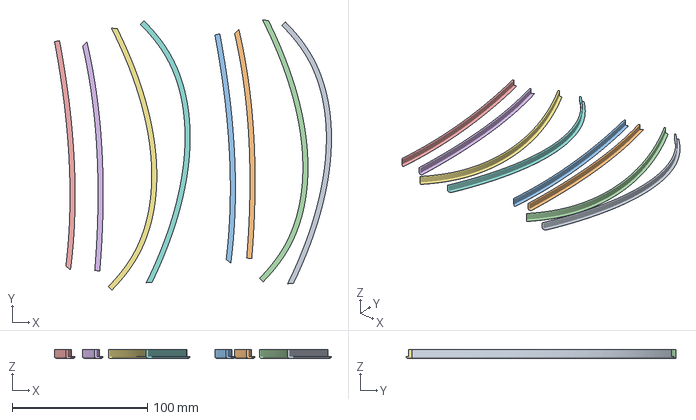
[picture p146: CAD file, 2025-05-30]
cad/SPP_InnerEdge_All.3mf
205.0 x 199.9 x 6.35 mm
SPP_InnerEdge_B_0.25.stl x 4
SPP_InnerEdge_A_0.25.stl x 4
