vizicist/spacepalettepro/cad/SPP_Edge_B_1.5_both.3mf

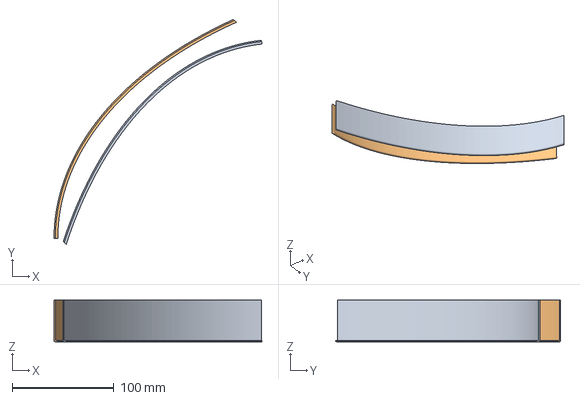
[picture p147: CAD file, 2025-05-30]
cad/SPP_Edge_B_1.5_both.3mf
204.1 x 220.8 x 40.8 mm
SPP_Edge_B_1.5.stl
SPP_Edge_B_1.5_flipped.stl
