vizicist/spacepalettepro/cad/SPP_arch.dxf

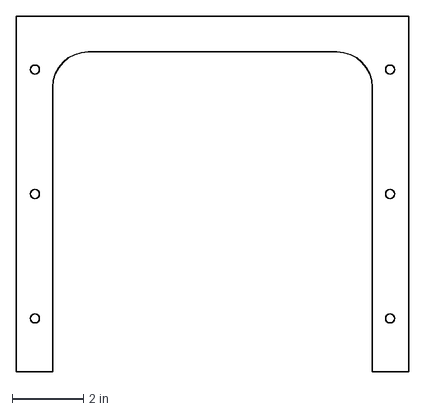
[picture p148: CAD file, 2025-05-30]
cad/SPP_arch.dxf
11.0 x 10.0 in
