vizicist/spacepalettepro/cad/SPP_headphonehook v11.stl

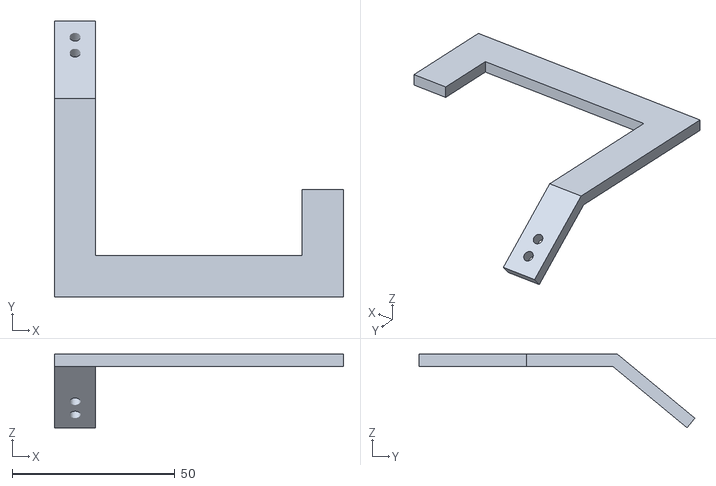
[picture p149: CAD file, 2025-05-30]
cad/SPP_headphonehook v11.stl
88.8 x 84.7 x 22.6
