vizicist/spacepalettepro/cad/SPP_side.dxf

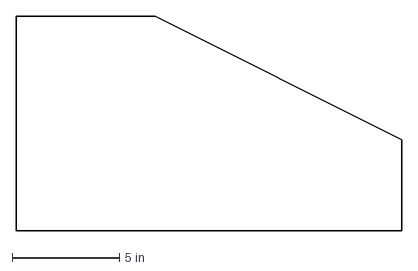
[picture p150: CAD file, 2025-05-30]
cad/SPP_side.dxf
18.0 x 10.00 in
