vizicist/spacepalettepro/cad/SPP_InnerEdge_A_0.25.stl

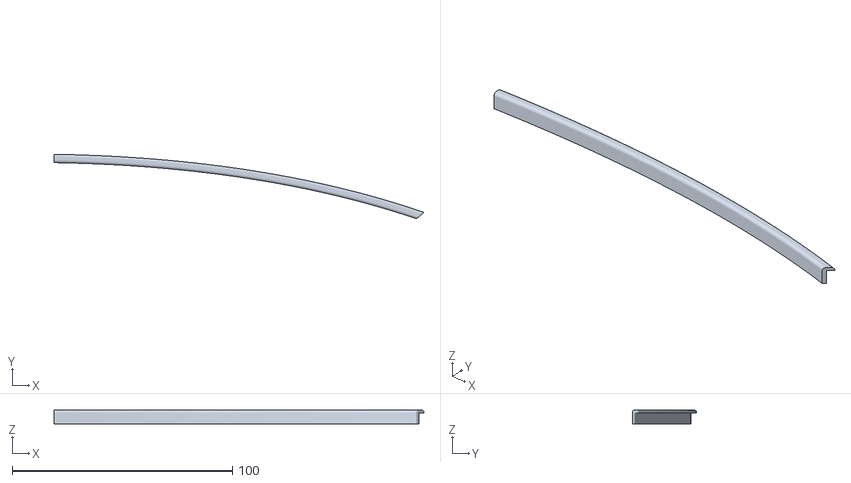
[picture p151: CAD file, 2025-05-30]
cad/SPP_InnerEdge_A_0.25.stl
167.9 x 29.2 x 6.35
