vizicist/spacepalettepro/cad/SPP_Edge_B_1.5.stl

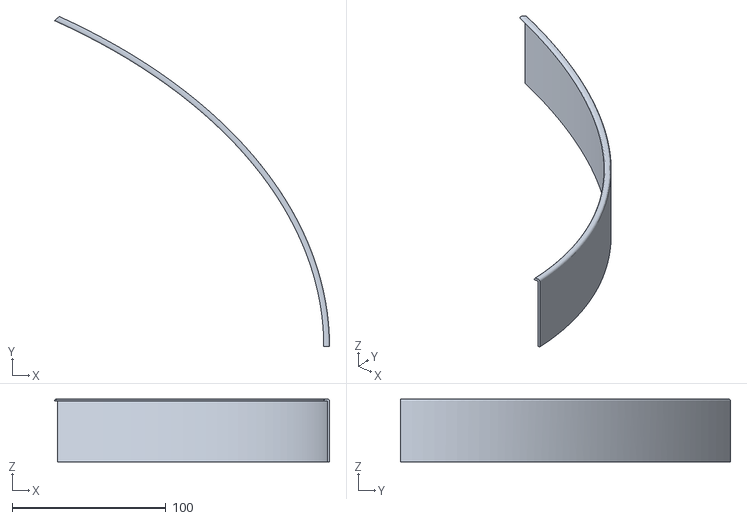
[picture p152: CAD file, 2025-05-30]
cad/SPP_Edge_B_1.5.stl
178.9 x 214.6 x 40.8
