vizicist/spacepalettepro/cad/SPP_sidesupport8test.3mf

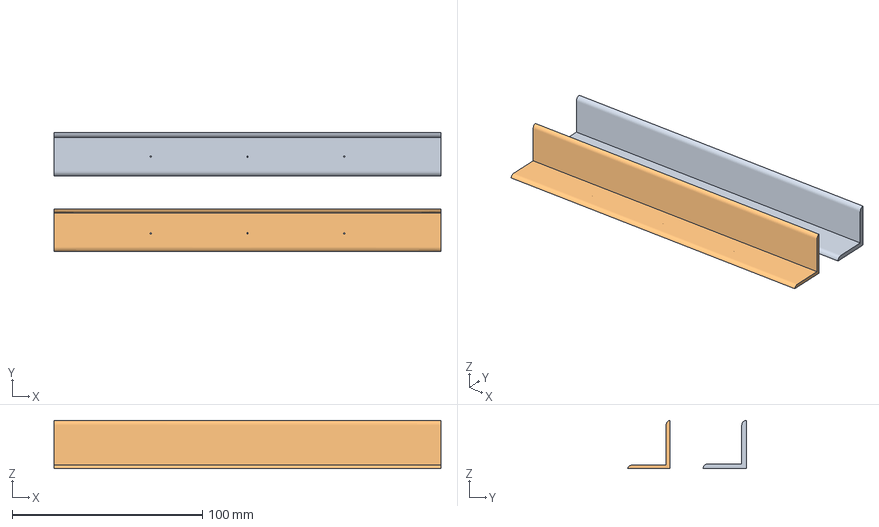
[picture p153: CAD file, 2025-05-30]
cad/SPP_sidesupport8test.3mf
203.2 x 62.5 x 25.4 mm
SPP_sidesupport8.stl
SPP_sidesupport8smaller.stl
