vizicist/spacepalettepro/cad/SPP_small_back.dxf

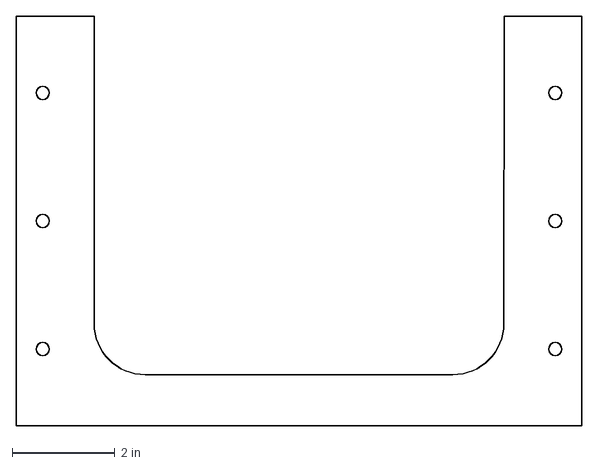
[picture p154: CAD file, 2025-05-30]
cad/SPP_small_back.dxf
11.0 x 8.00 in
