vizicist/spacepalettepro/cad/SPP_morph_outline.3mf

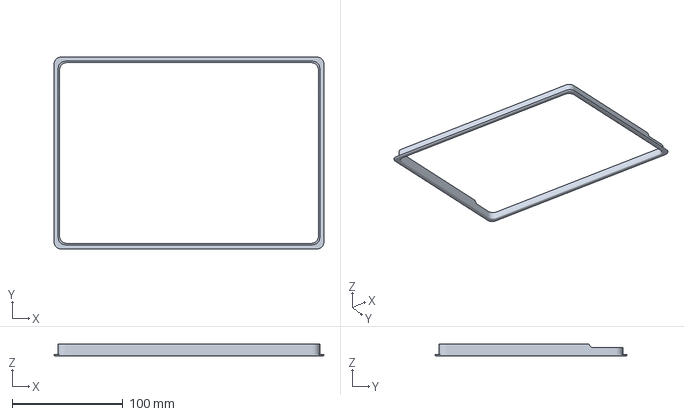
[picture p155: CAD file, 2025-05-30]
cad/SPP_morph_outline.3mf
243.7 x 173.3 x 10.8 mm
