vizicist/spacepalettepro/cad/SPP_Edge_A_1.5_flipped.3mf

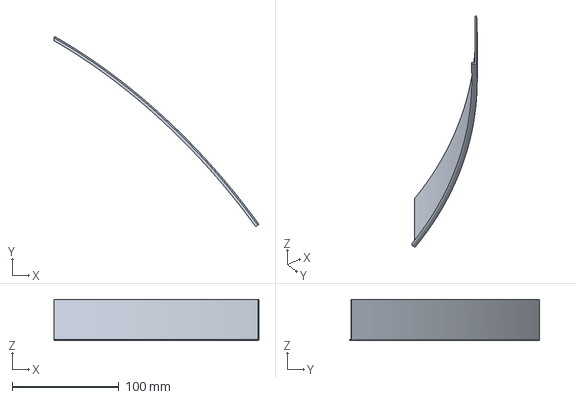
[picture p156: CAD file, 2025-05-30]
cad/SPP_Edge_A_1.5_flipped.3mf
192.4 x 178.7 x 38.9 mm
