vizicist/spacepalettepro/cad/SPP_SideHeadphone.3mf

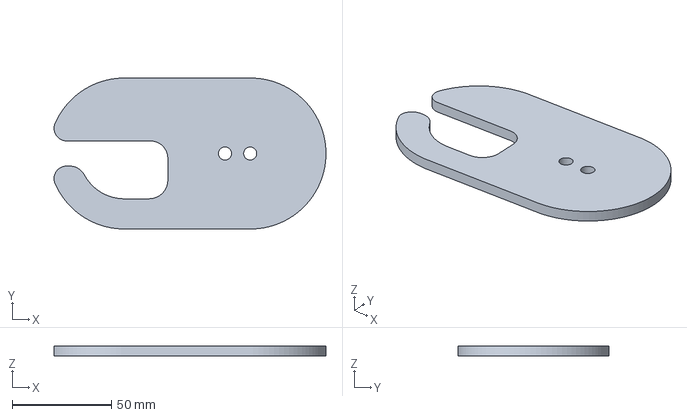
[picture p157: CAD file, 2025-05-30]
cad/SPP_SideHeadphone.3mf
137.2 x 76.2 x 5.08 mm
