vizicist/spacepalettepro/cad/SPP_InnerSupport.3mf

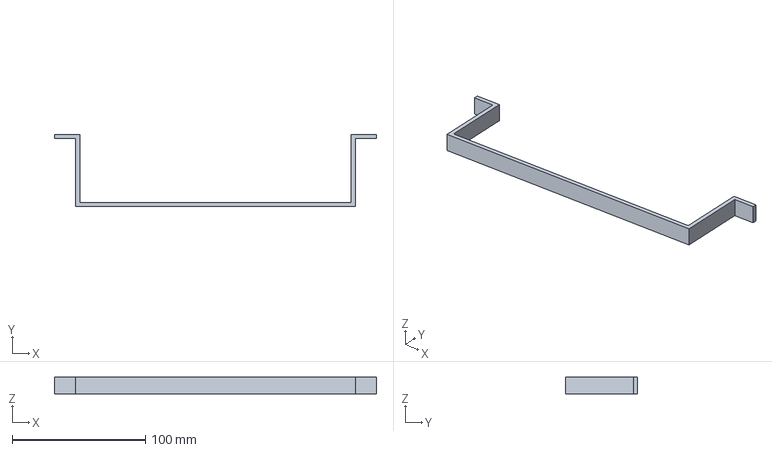
[picture p158: CAD file, 2025-05-30]
cad/SPP_InnerSupport.3mf
241.3 x 54.0 x 12.7 mm
