vizicist/spacepalettepro/cad/SPP_headphonehookA.3mf

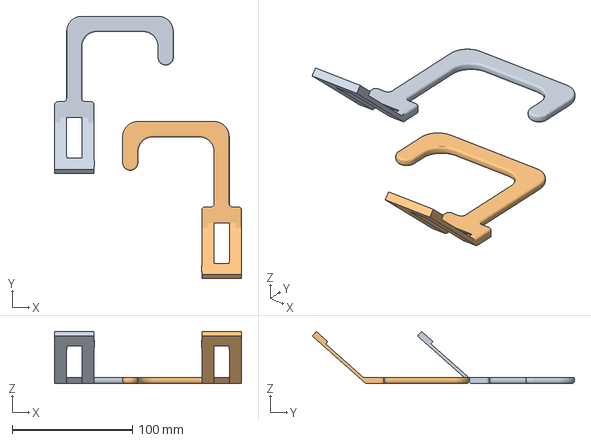
[picture p159: CAD file, 2025-05-30]
cad/SPP_headphonehookA.3mf
155.7 x 218.5 x 43.3 mm
SPP_headphonehookA.stl x 2
