vizicist/spacepalettepro/cad/SPP_Edge_B_0.25_flipped.stl

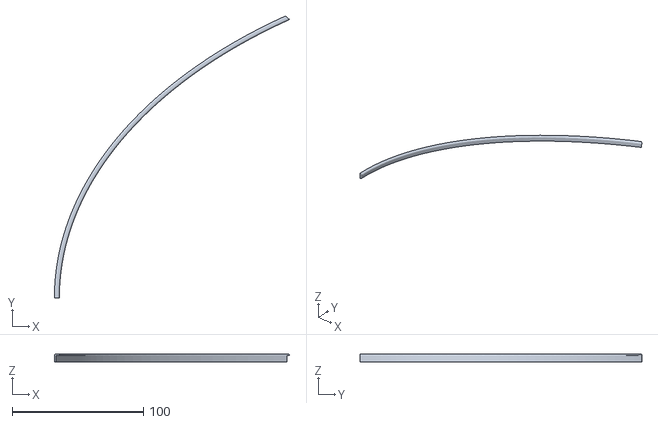
[picture p160: CAD file, 2025-05-30]
cad/SPP_Edge_B_0.25_flipped.stl
179.1 x 214.6 x 6.35
