vizicist/spacepalettepro/cad/SPP_Edge_A_1.5.3mf

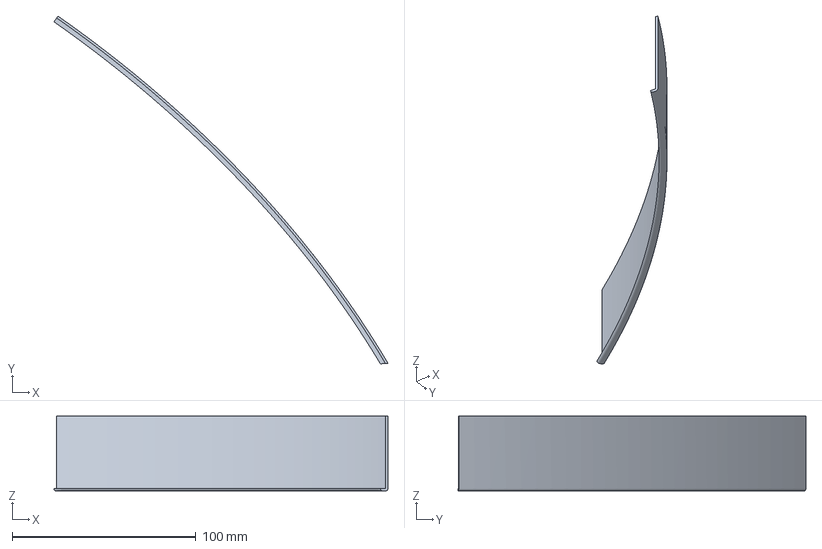
[picture p161: CAD file, 2025-05-30]
cad/SPP_Edge_A_1.5.3mf
182.0 x 189.5 x 40.8 mm
