vizicist/spacepalettepro/cad/SPP_MonLayer2_3_bottomb.dxf

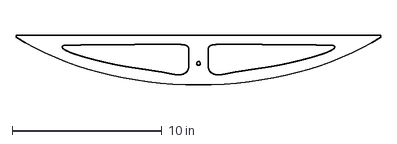
[picture p162: CAD file, 2025-01-19]
cad/SPP_MonLayer2_3_bottomb.dxf
24.4 x 3.31 in
