vizicist/spacepalettepro/cad/SPP_MonLayer2_3_leftrightb.dxf

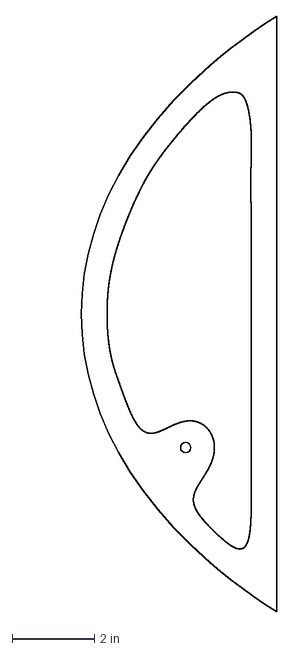
[picture p163: CAD file, 2025-01-19]
cad/SPP_MonLayer2_3_leftrightb.dxf
6.34 x 14.5 in
