vizicist/spacepalettepro/cad/SPP_Monlayer4b.dxf

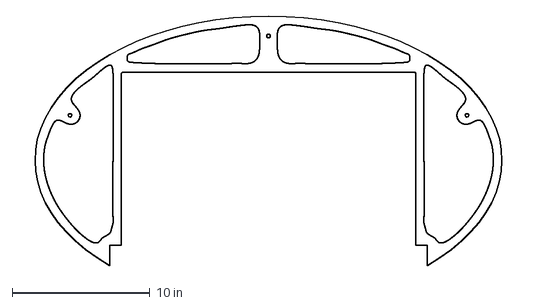
[picture p164: CAD file, 2025-01-19]
cad/SPP_Monlayer4b.dxf
36.6 x 18.1 in
