vizicist/spacepalettepro/cad/SPP_MonLayer2_3_topb.dxf

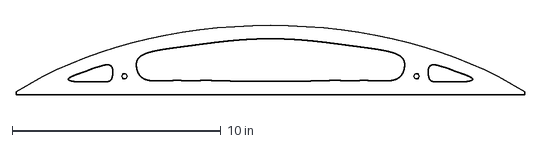
[picture p165: CAD file, 2025-01-19]
cad/SPP_MonLayer2_3_topb.dxf
24.4 x 3.31 in
