vizicist/spacepalettepro/cad/SPP_MonLayer5b.dxf

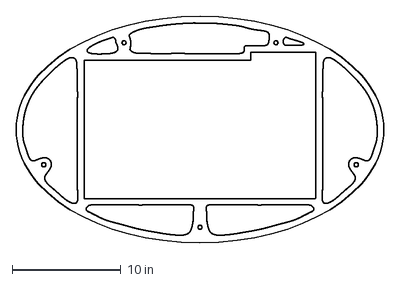
[picture p166: CAD file, 2025-01-19]
cad/SPP_MonLayer5b.dxf
33.9 x 20.9 in
