vizicist/spacepalettepro/cad/SPP_Layer7_Backb.dxf

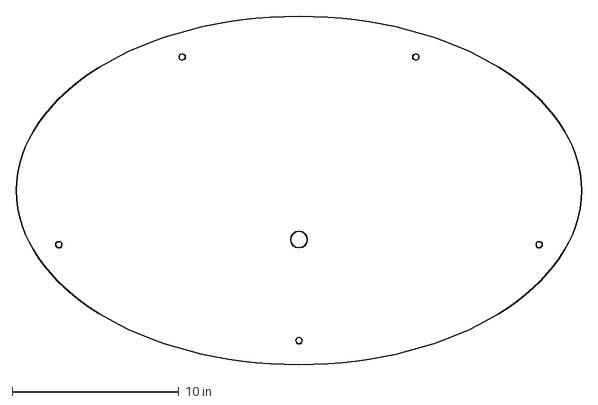
[picture p167: CAD file, 2025-01-19]
cad/SPP_Layer7_Backb.dxf
33.9 x 20.9 in
