vizicist/spacepalettepro/cad/SPP_MonLayer6_back.dxf

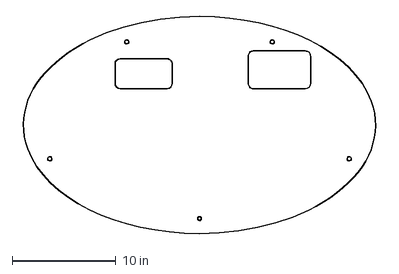
[picture p168: CAD file, 2021-08-06]
cad/SPP_MonLayer6_back.dxf
35.3 x 20.9 in
