vizicist/spacepalettepro/images/building_base/IMG_6318.jpg

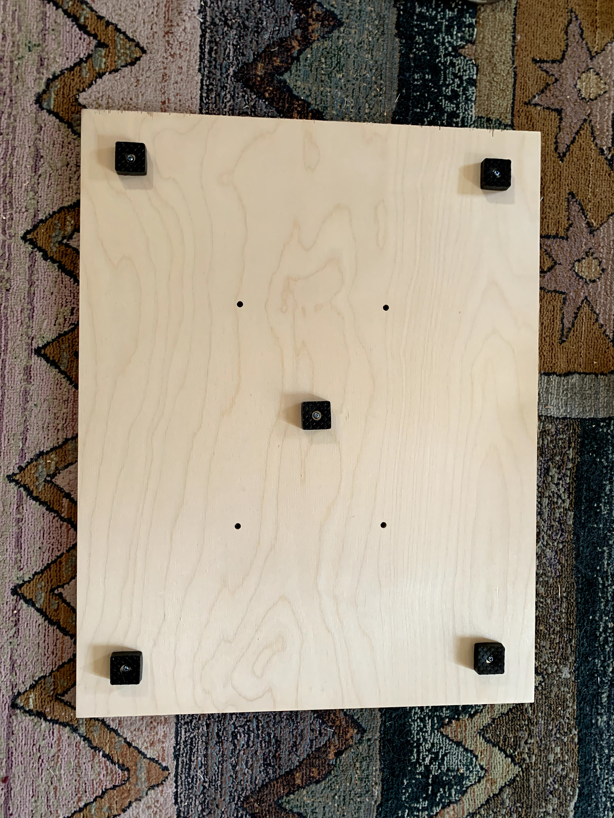
images/building_base/IMG_6318.jpg
