vizicist/spacepalettepro/images/building_base/IMG_6326.jpg

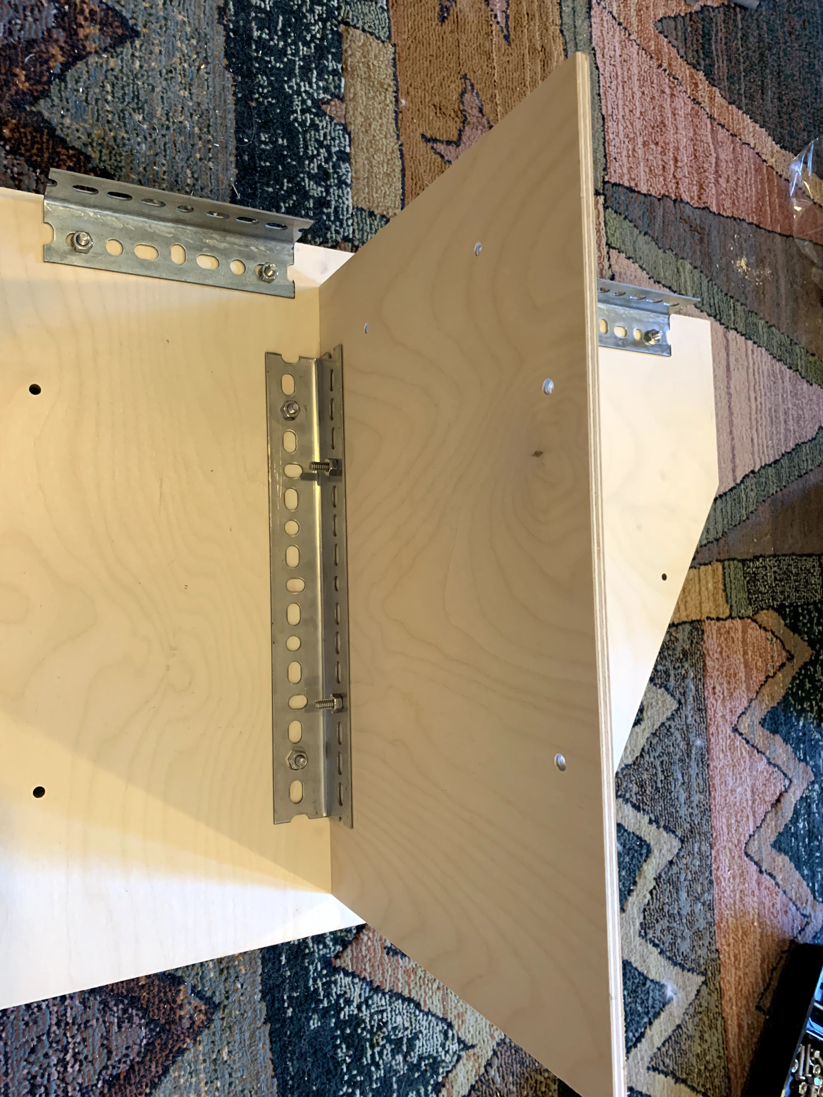
images/building_base/IMG_6326.jpg
