vizicist/spacepalettepro/images/building_base/IMG_6333.jpg

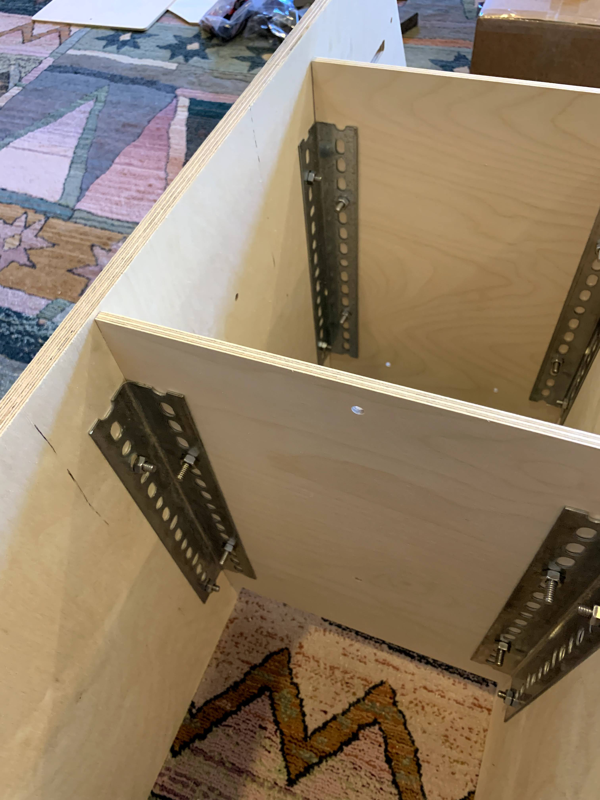
images/building_base/IMG_6333.jpg
