vizicist/spacepalettepro/images/building_base/IMG_6334.jpg

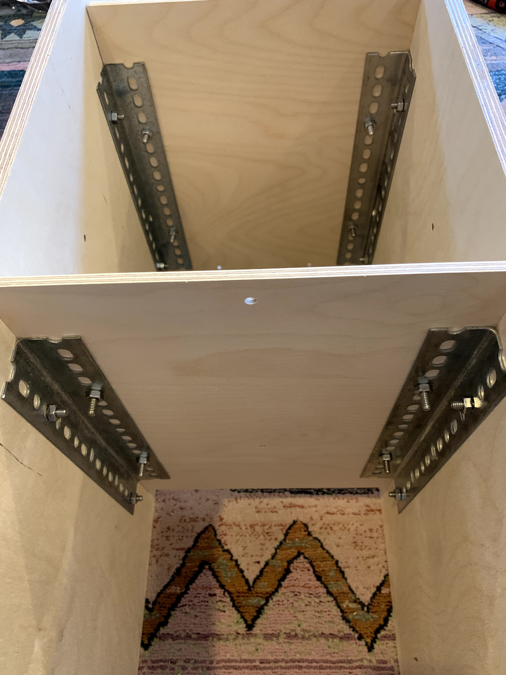
images/building_base/IMG_6334.jpg
