vizicist/spacepalettepro/images/building_base/IMG_6337.jpg

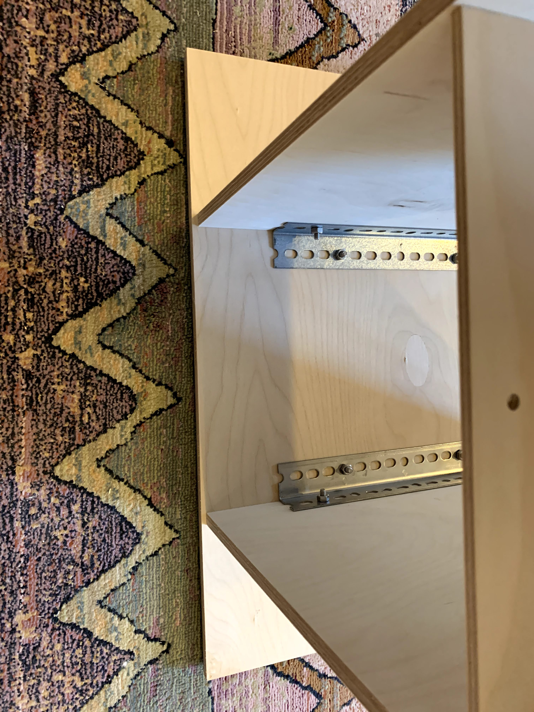
images/building_base/IMG_6337.jpg
