vizicist/spacepalettepro/images/building_base/IMG_6339.jpg

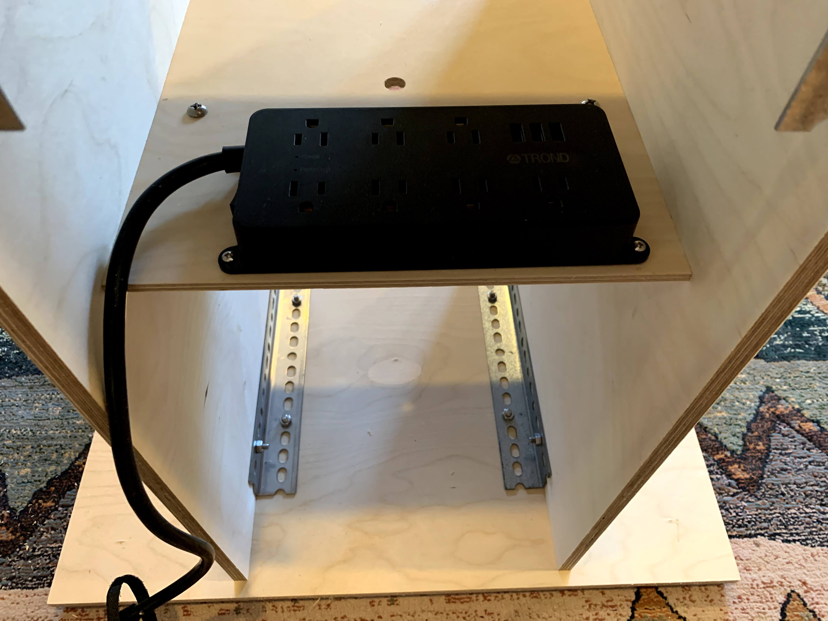
images/building_base/IMG_6339.jpg
