vizicist/spacepalettepro/images/building_base/IMG_6341.jpg

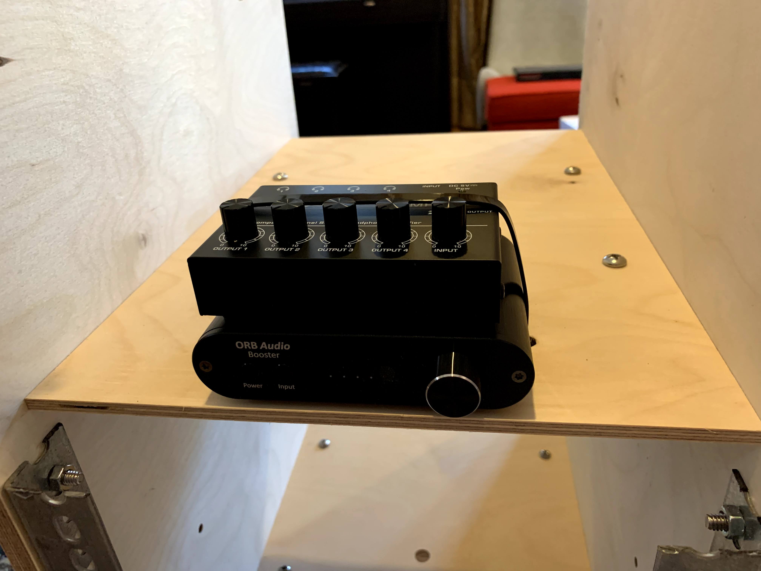
images/building_base/IMG_6341.jpg
