vizicist/spacepalettepro/images/building_base/IMG_6343.jpg

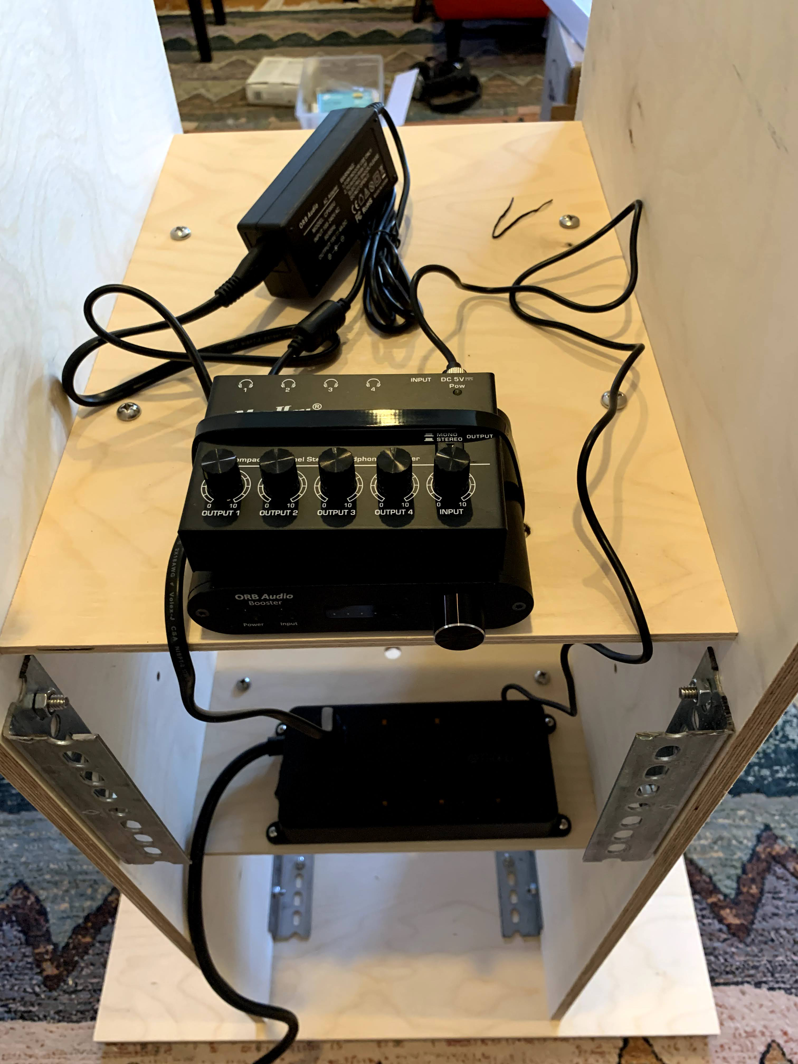
images/building_base/IMG_6343.jpg
