vizicist/spacepalettepro/images/building_base/IMG_6345.jpg

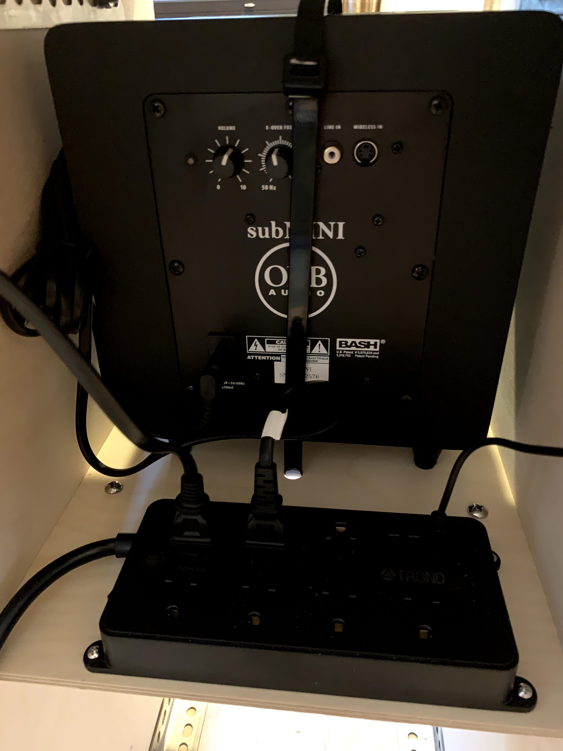
images/building_base/IMG_6345.jpg
