vizicist/spacepalettepro/images/building_base/IMG_6346.jpg

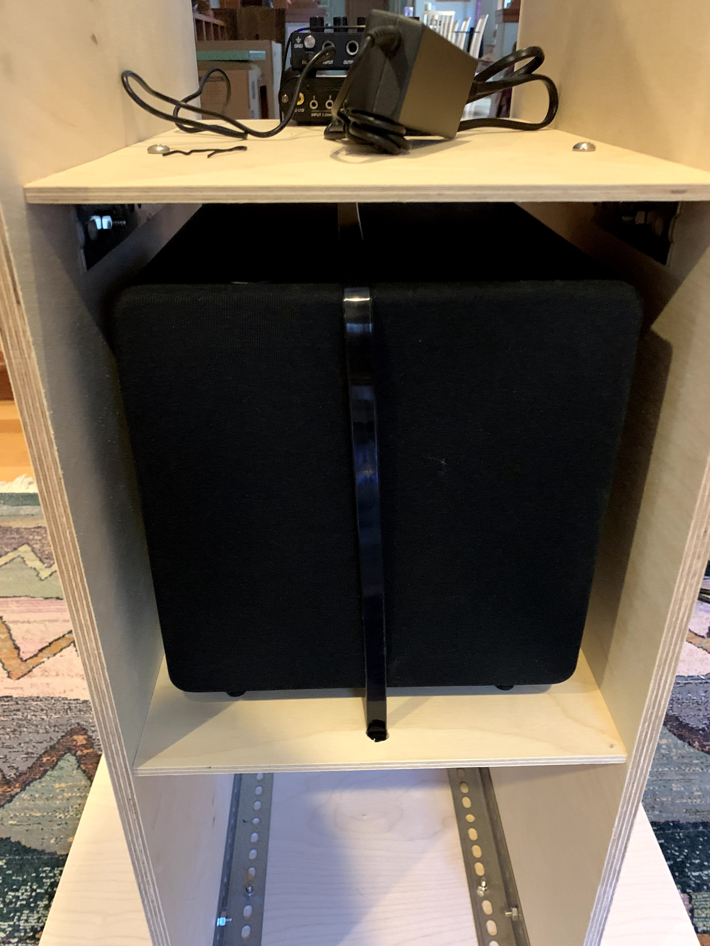
images/building_base/IMG_6346.jpg
