vizicist/spacepalettepro/images/building_base/IMG_6349.jpg

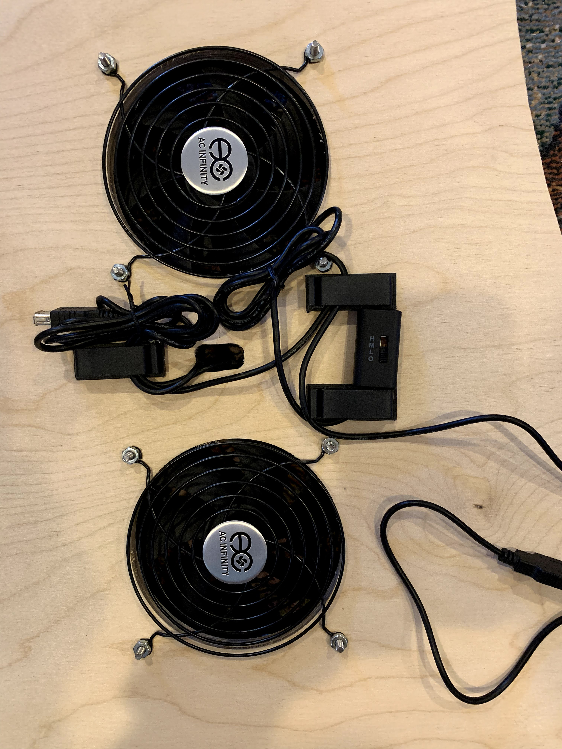
images/building_base/IMG_6349.jpg
