vizicist/spacepalettepro/images/building_base/IMG_6580.jpg

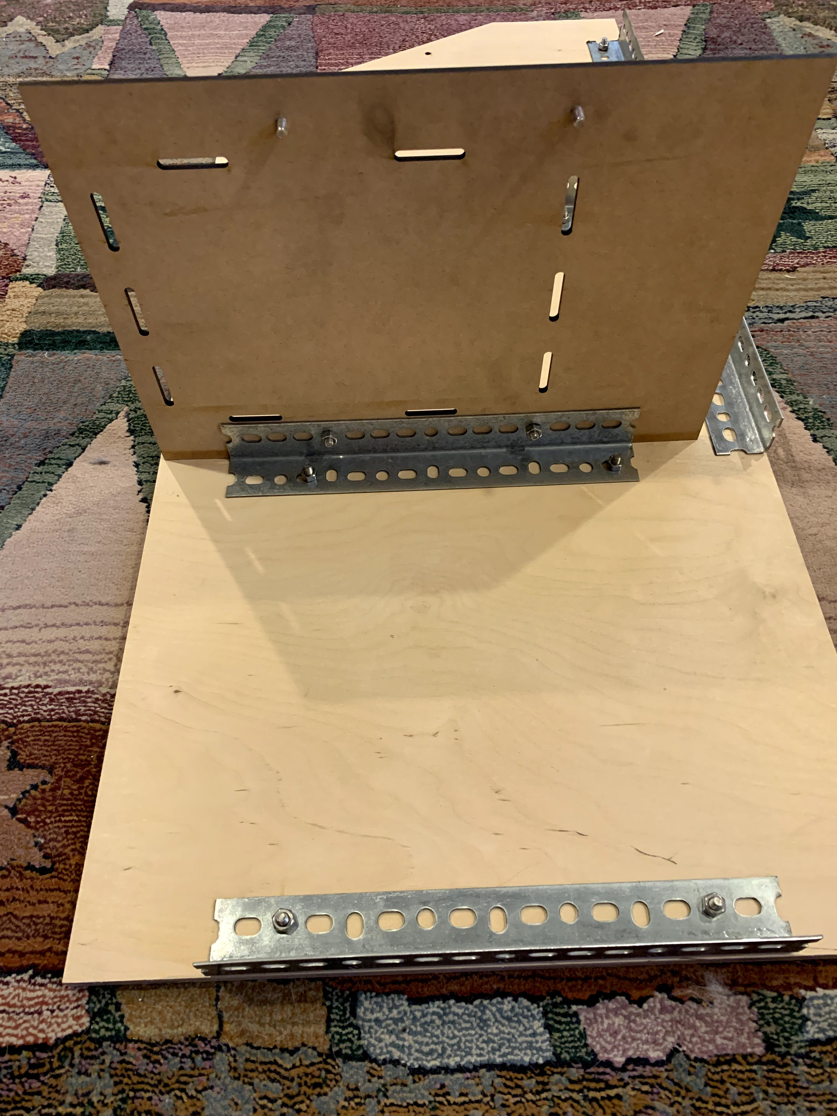
images/building_base/IMG_6580.jpg
