vizicist/spacepalettepro/images/building_base/IMG_6581.jpg

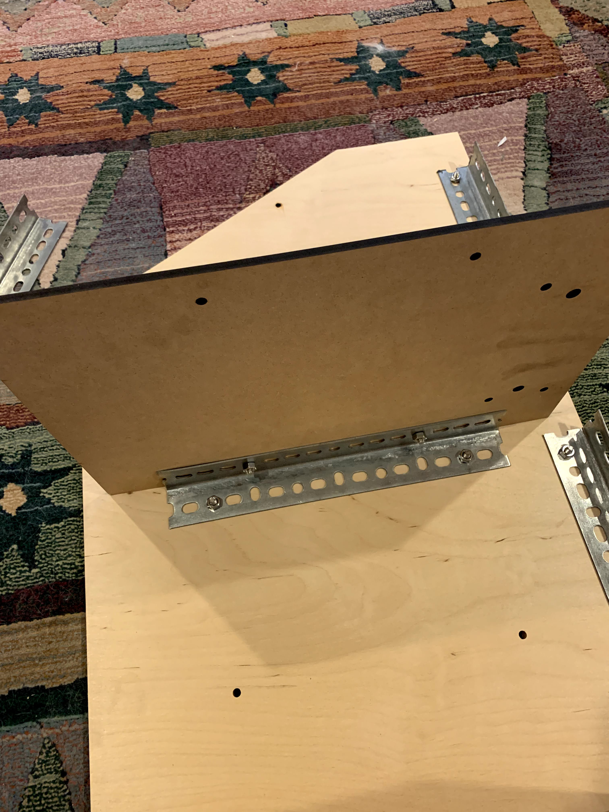
images/building_base/IMG_6581.jpg
