vizicist/spacepalettepro/images/building_base/IMG_6598.jpg

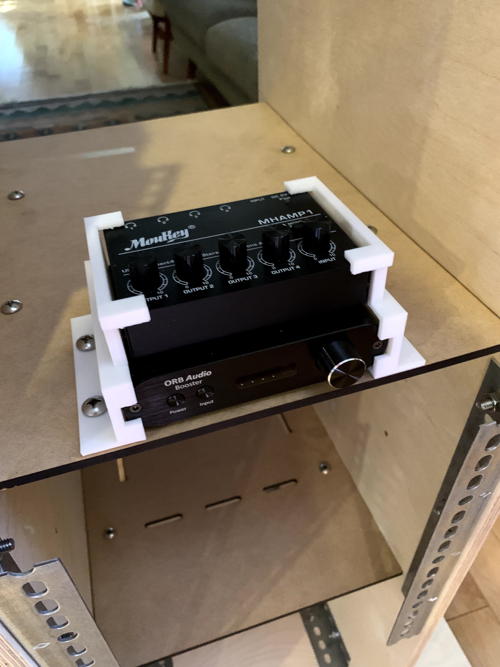
images/building_base/IMG_6598.jpg
