vizicist/spacepalettepro/images/building_base/IMG_6600.jpg

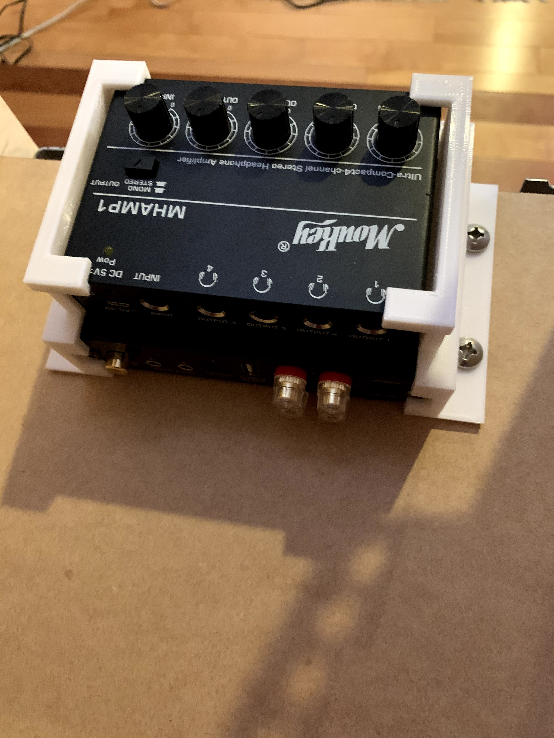
images/building_base/IMG_6600.jpg
