vizicist/spacepalettepro/images/building_controller/IMG_6261.jpg

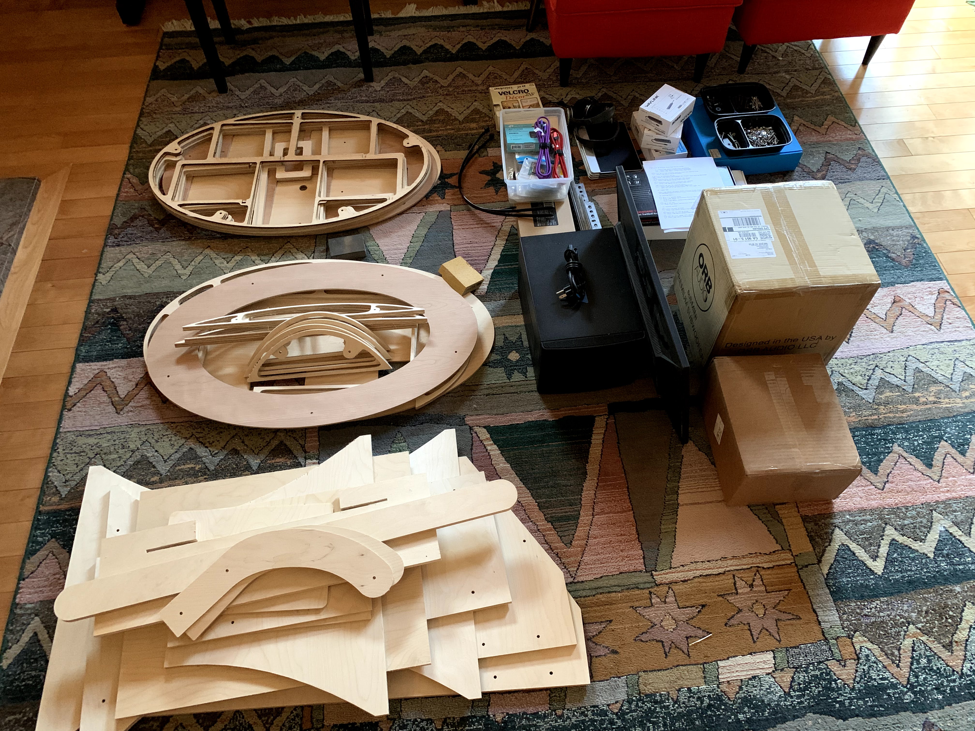
images/building_controller/IMG_6261.jpg
