vizicist/spacepalettepro/images/building_controller/IMG_6298.jpg

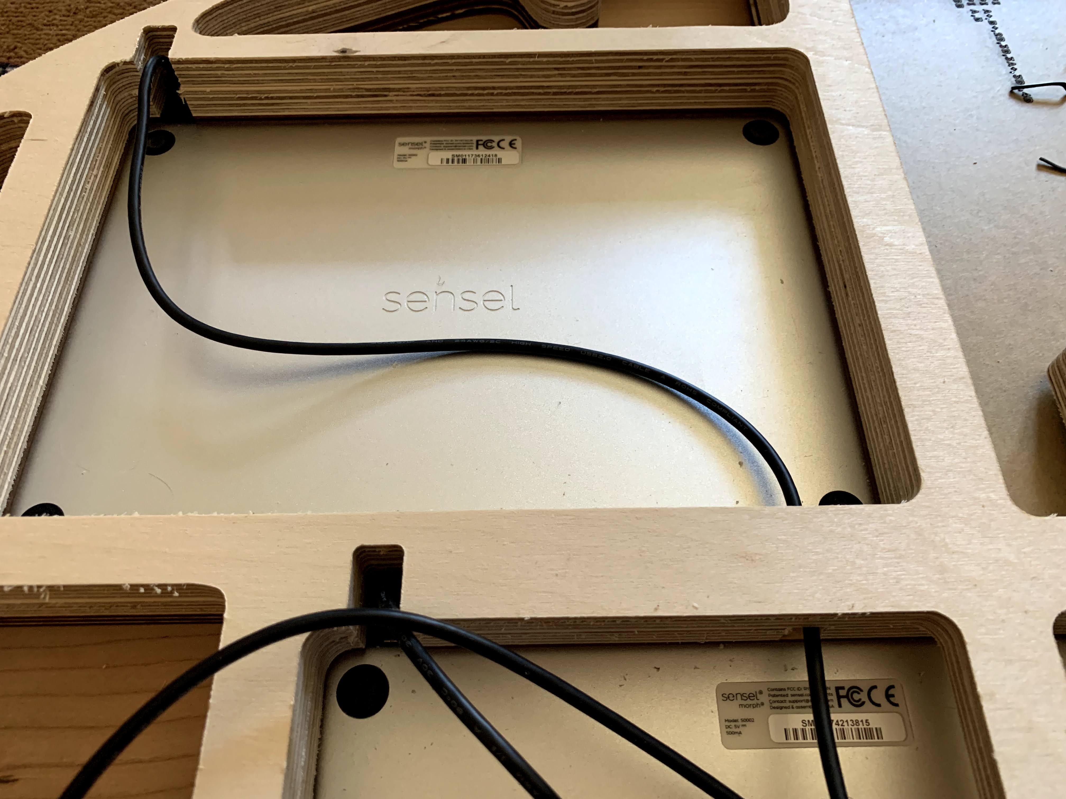
images/building_controller/IMG_6298.jpg
