vizicist/spacepalettepro/images/building_controller/IMG_6299.jpg

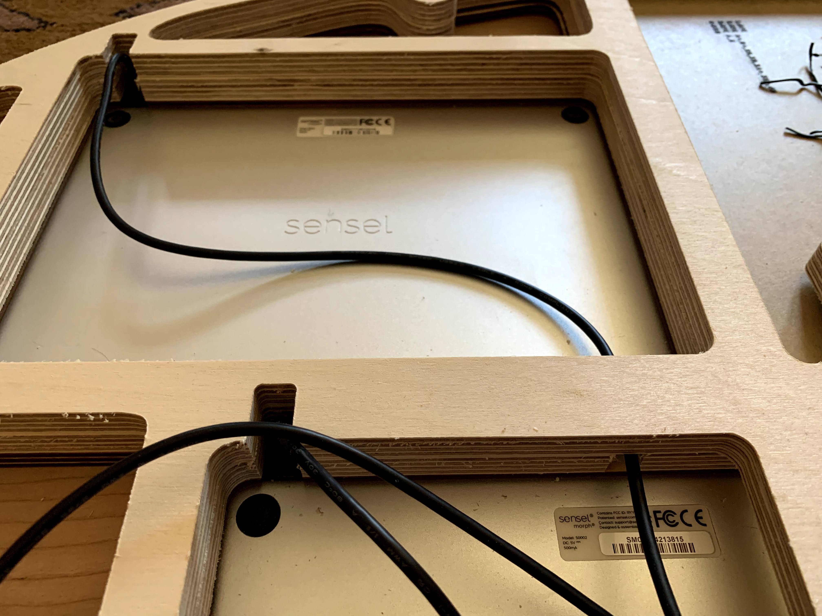
images/building_controller/IMG_6299.jpg
