vizicist/spacepalettepro/images/building_controller/IMG_6300.jpg

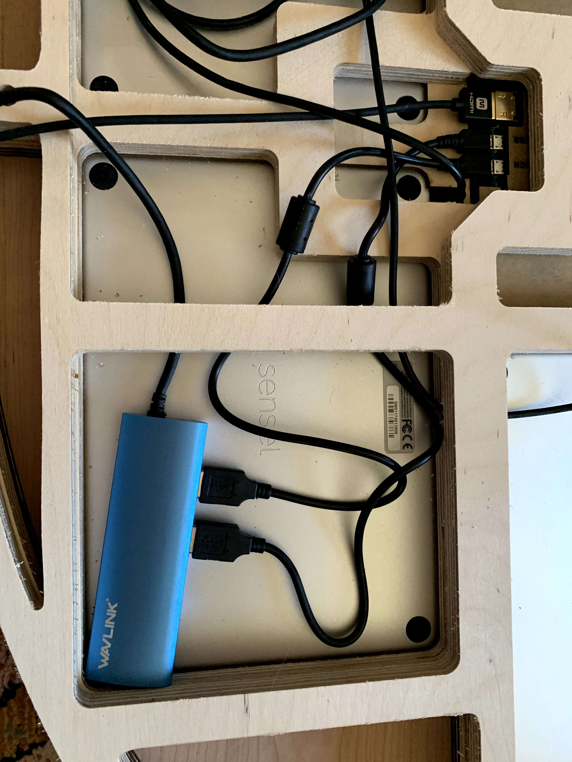
images/building_controller/IMG_6300.jpg
