vizicist/spacepalettepro/images/building_base/IMG_6322.jpg

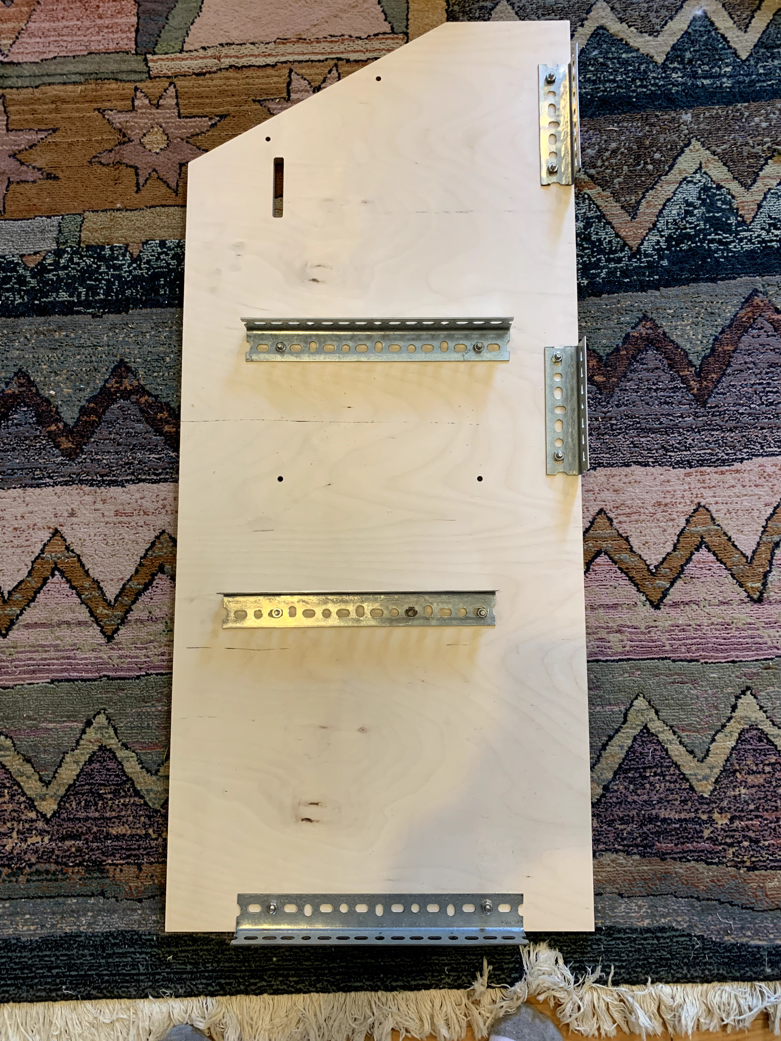
images/building_base/IMG_6322.jpg
