vizicist/spacepalettepro/images/building_base/IMG_6323.jpg

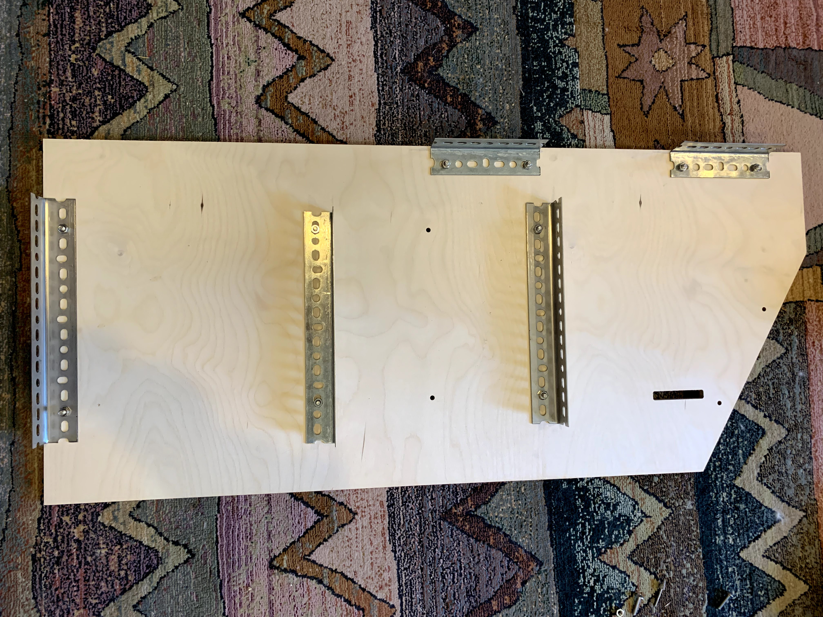
images/building_base/IMG_6323.jpg
