vizicist/spacepalettepro/images/building_base/IMG_6324.jpg

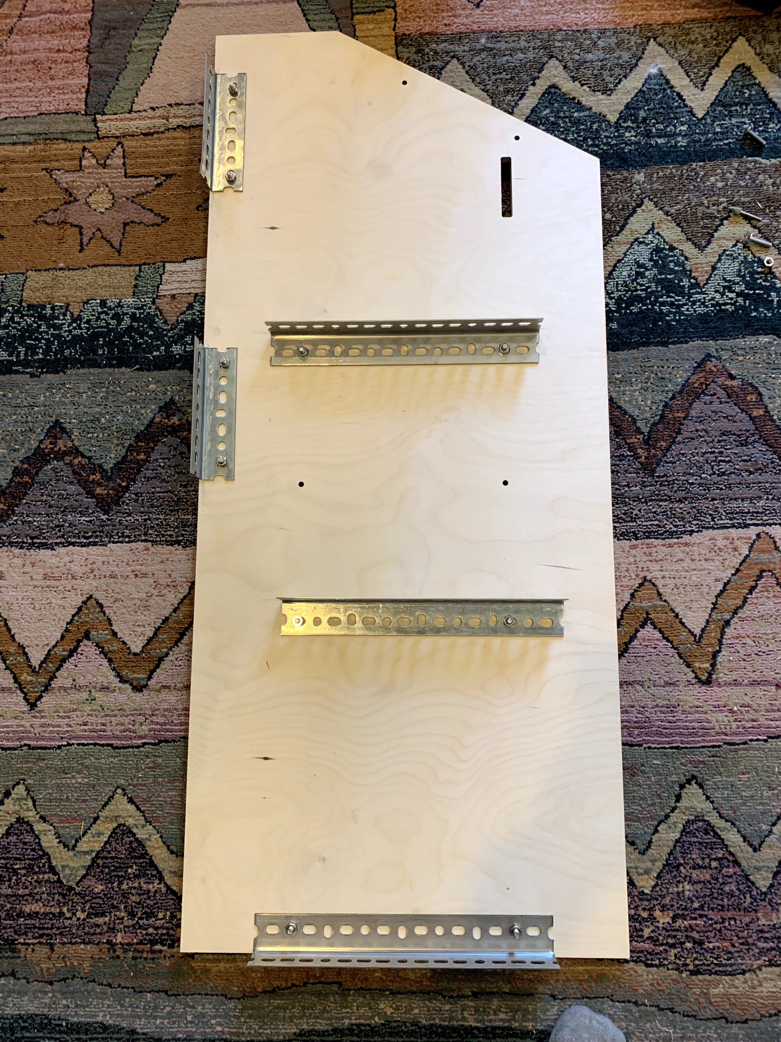
images/building_base/IMG_6324.jpg
