vizicist/spacepalettepro/images/building_base/IMG_6330.jpg

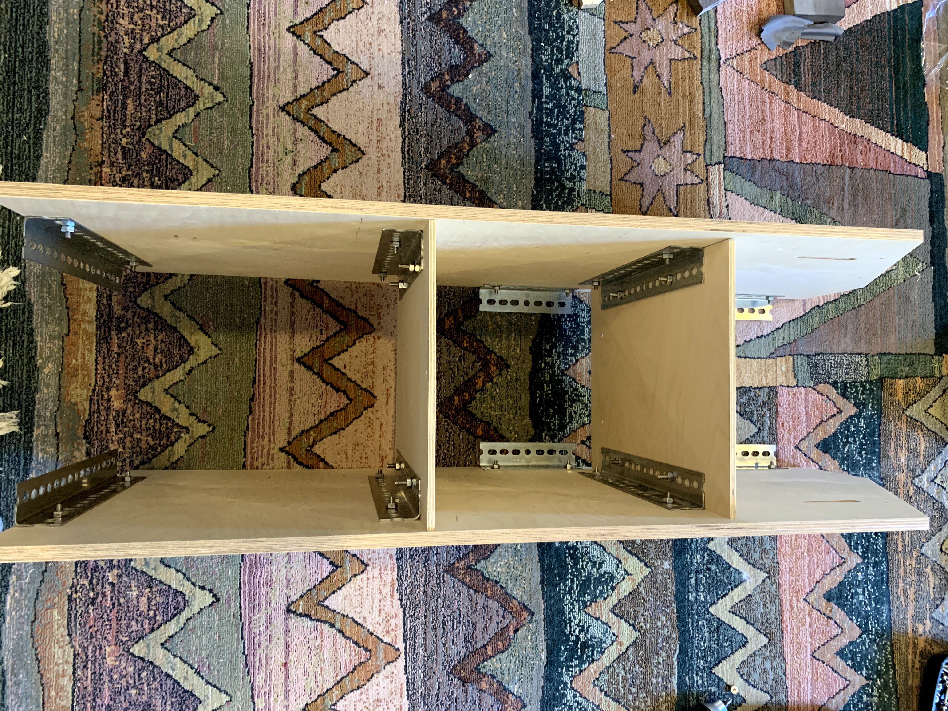
images/building_base/IMG_6330.jpg
