vizicist/spacepalettepro/images/building_base/IMG_6331.jpg

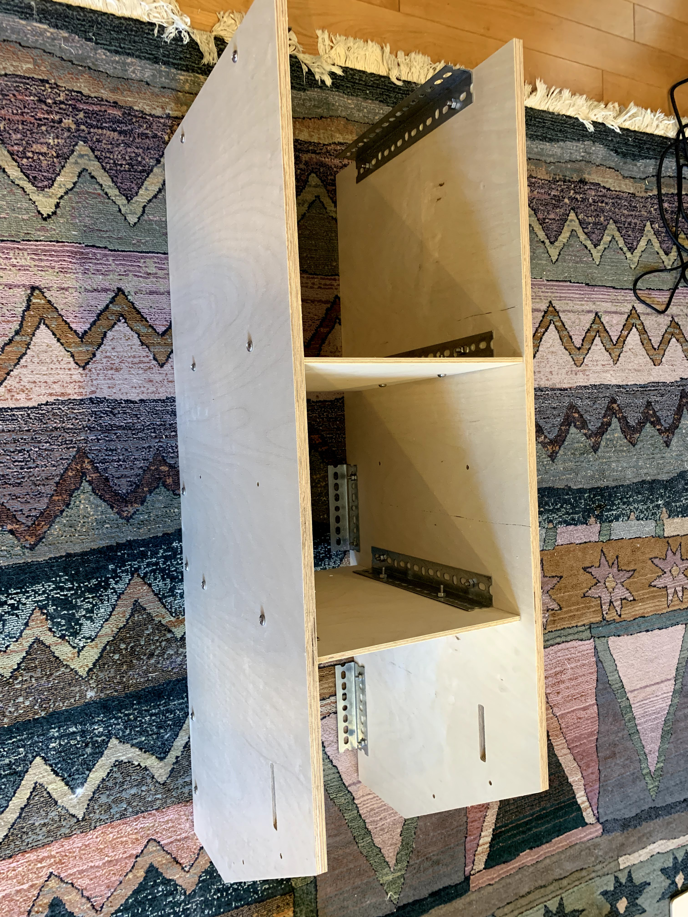
images/building_base/IMG_6331.jpg
