vizicist/spacepalettepro/images/building_base/IMG_6332.jpg

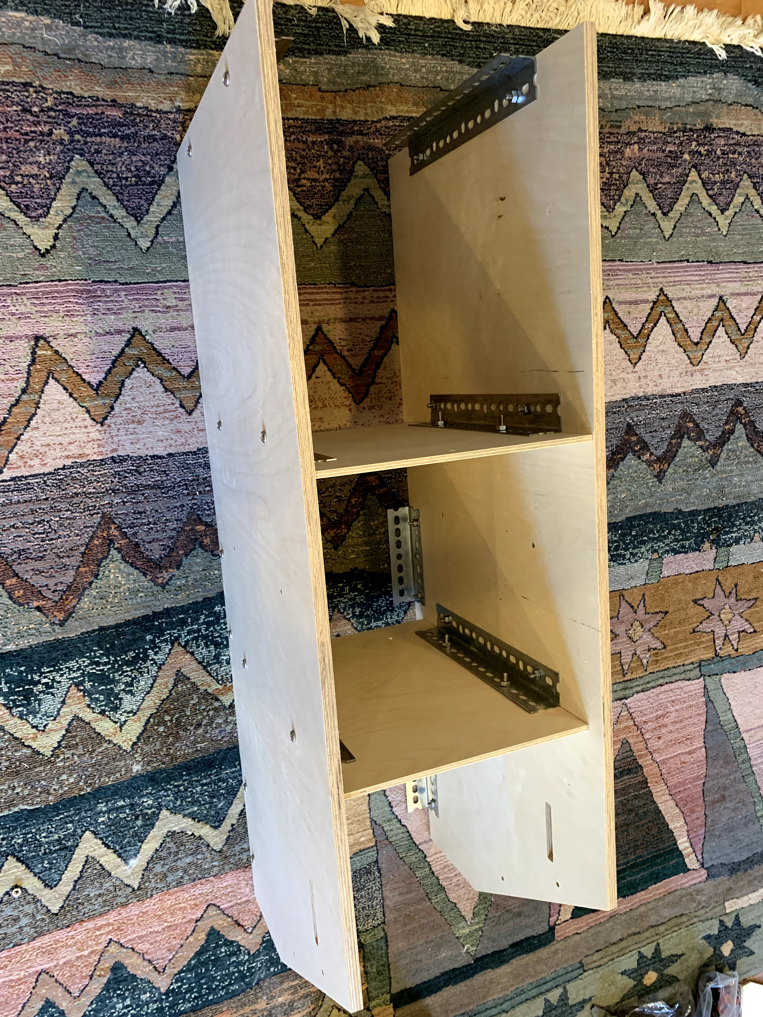
images/building_base/IMG_6332.jpg
