vizicist/spacepalettepro/images/building_base/IMG_6335.jpg

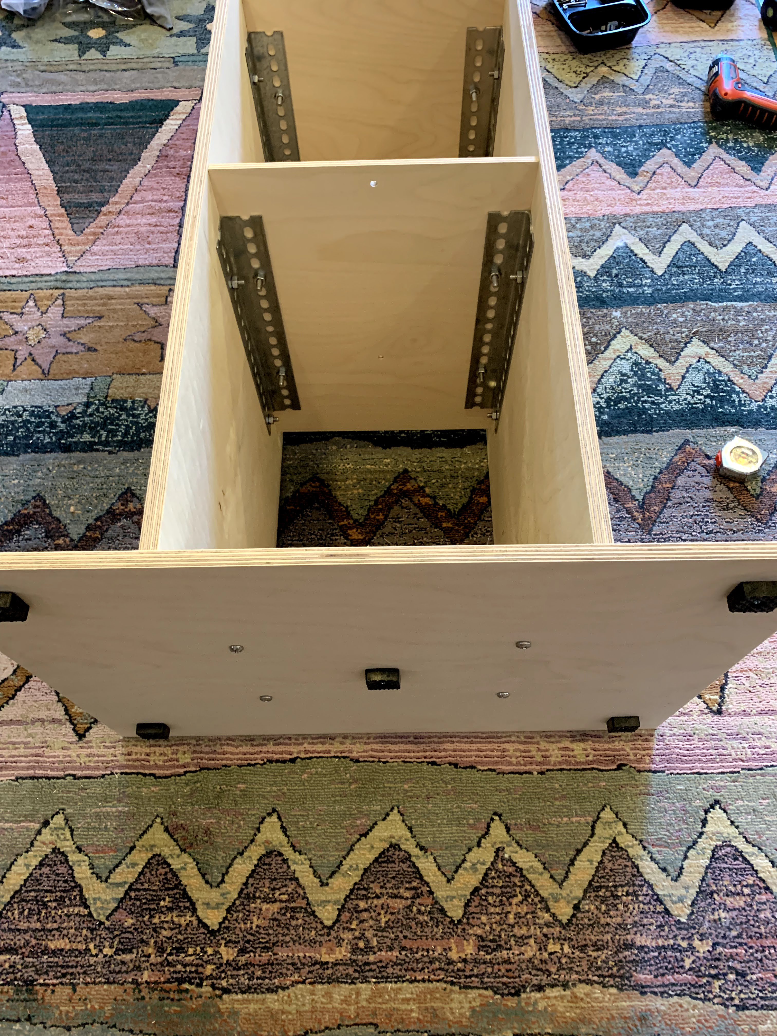
images/building_base/IMG_6335.jpg
