vizicist/spacepalettepro/images/building_base/IMG_6336.jpg

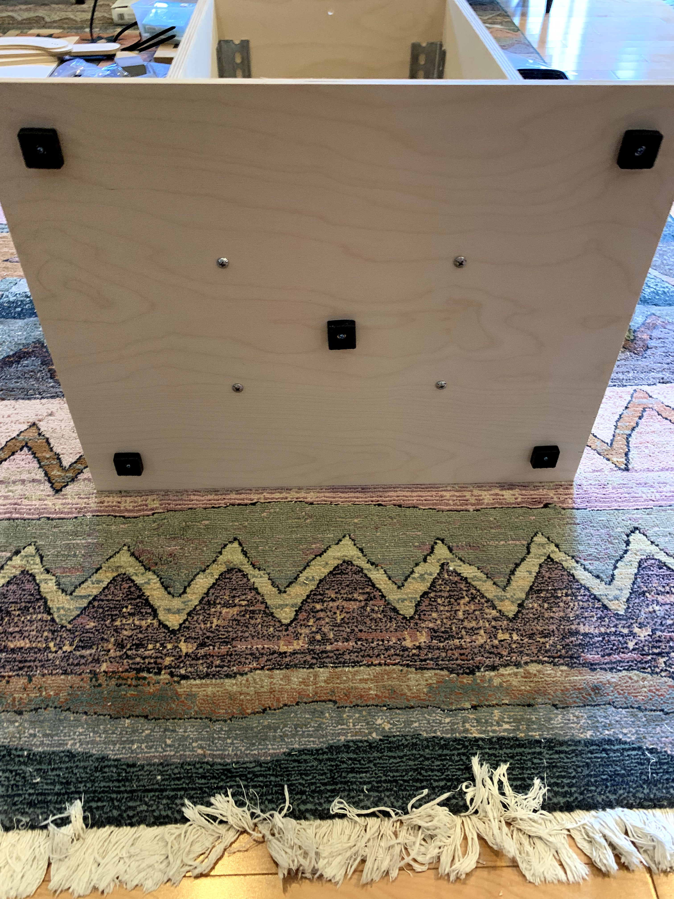
images/building_base/IMG_6336.jpg
