vizicist/spacepalettepro/images/building_base/IMG_6338.jpg

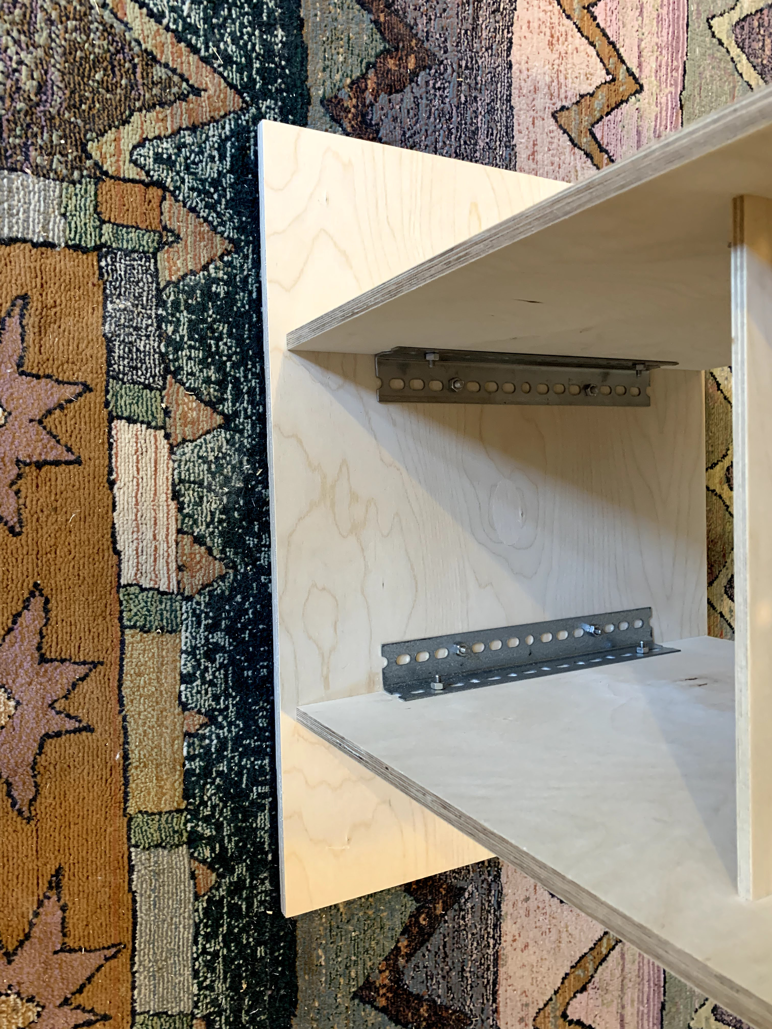
images/building_base/IMG_6338.jpg
