vizicist/spacepalettepro/images/building_base/IMG_6344.jpg

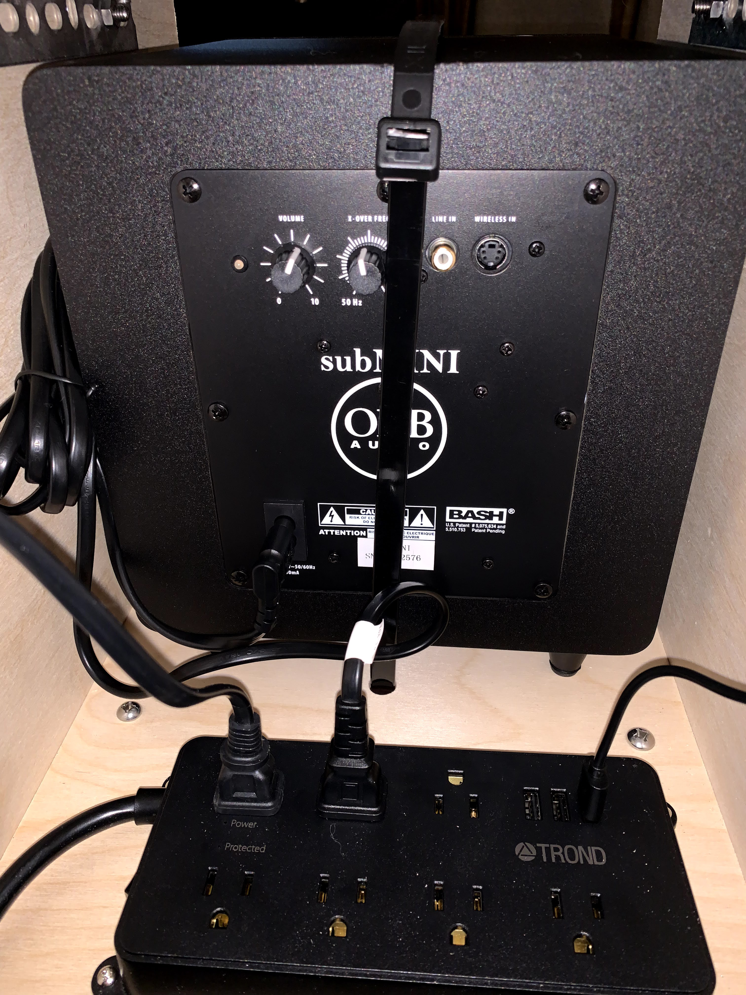
images/building_base/IMG_6344.jpg
