vizicist/spacepalettepro/images/building_base/IMG_6347.jpg

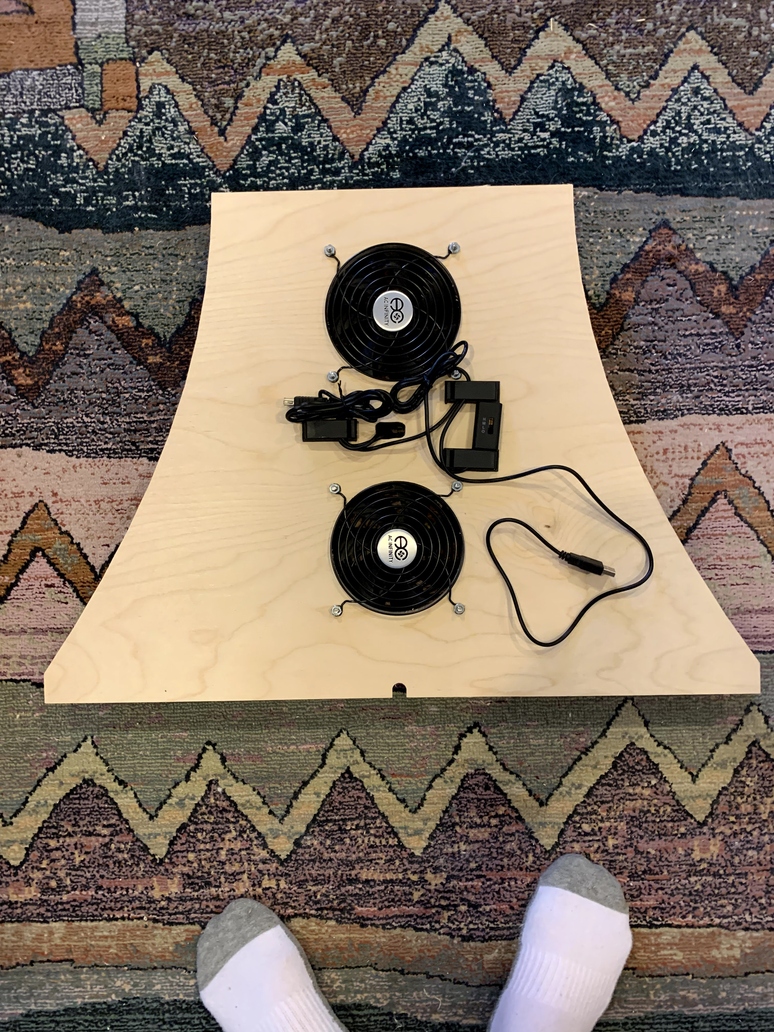
images/building_base/IMG_6347.jpg
