vizicist/spacepalettepro/images/building_base/IMG_6350.jpg

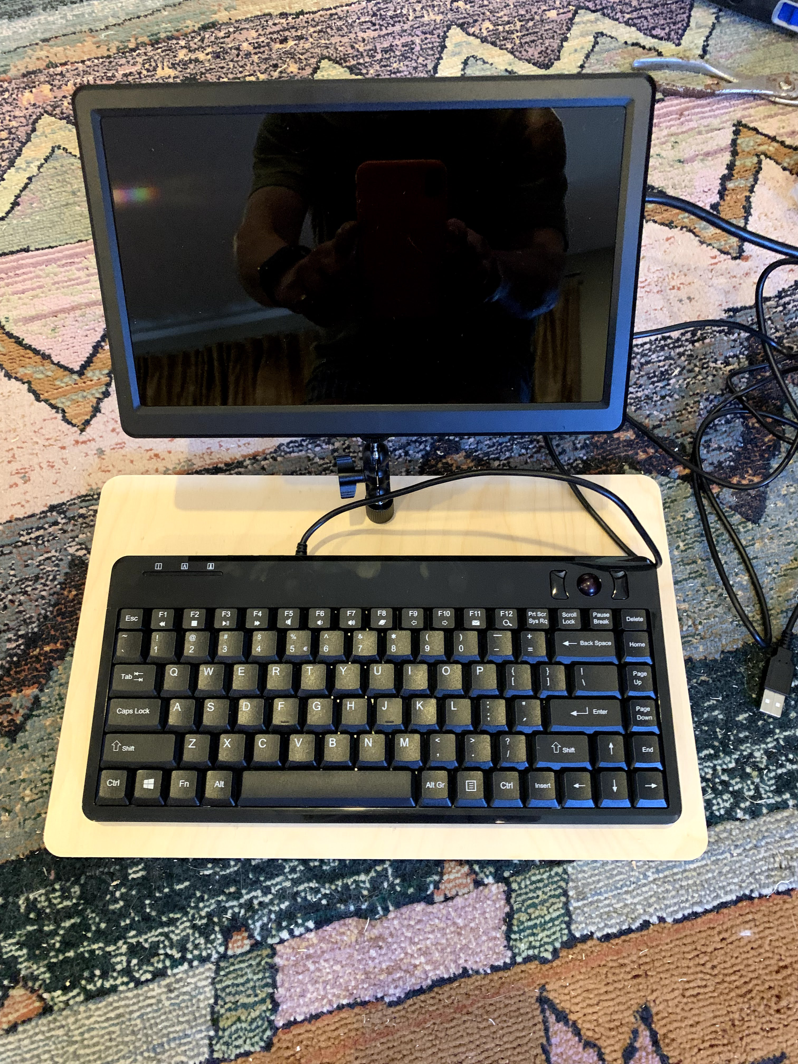
images/building_base/IMG_6350.jpg
