vizicist/spacepalettepro/images/building_base/IMG_6352.jpg

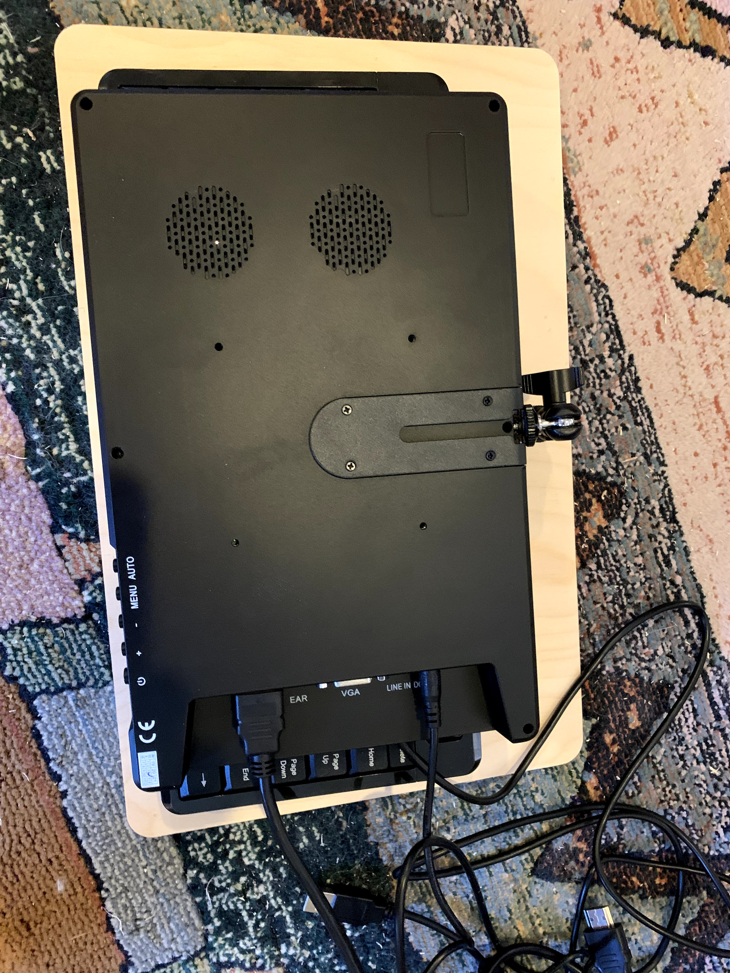
images/building_base/IMG_6352.jpg
