vizicist/spacepalettepro/images/building_base/IMG_6579.jpg

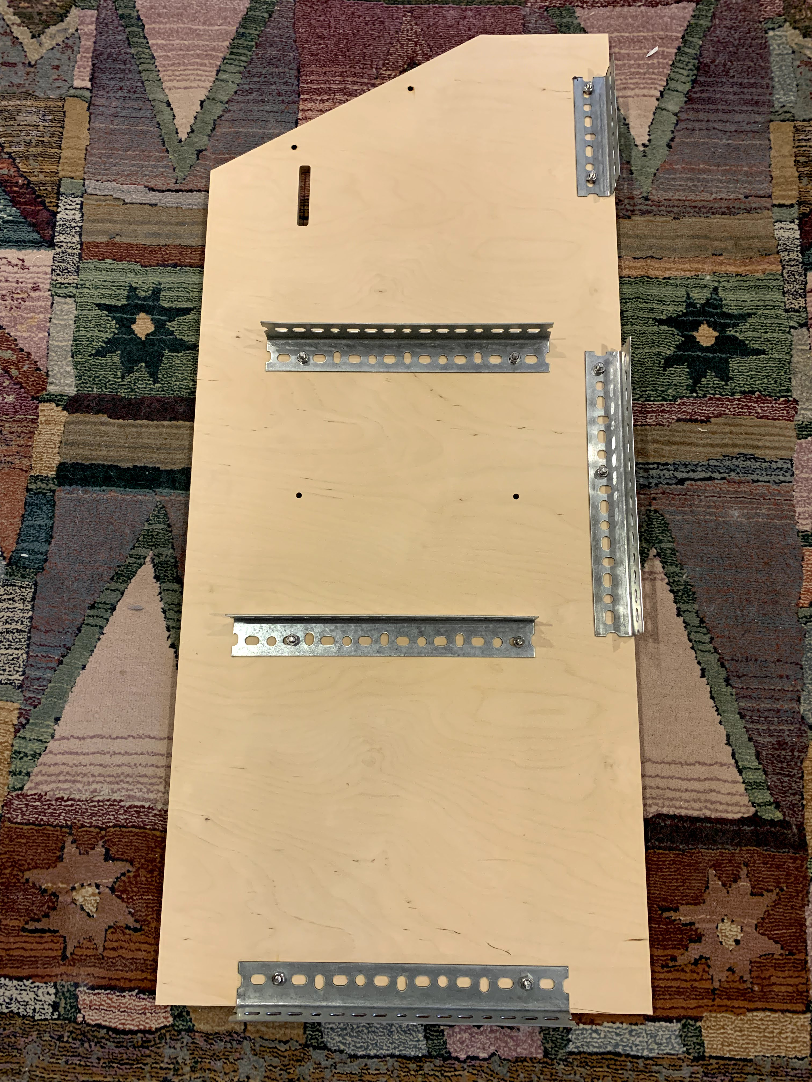
images/building_base/IMG_6579.jpg
