vizicist/spacepalettepro/images/building_base/IMG_6582.jpg

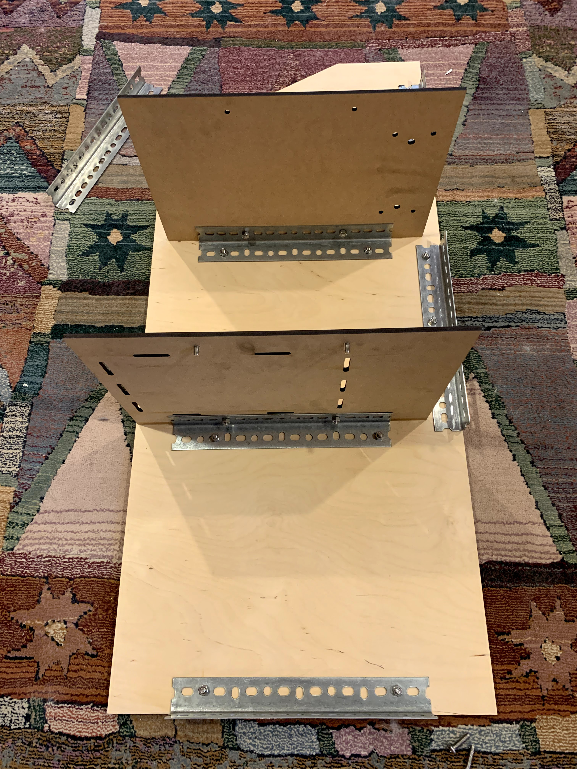
images/building_base/IMG_6582.jpg
