vizicist/spacepalettepro/images/building_base/IMG_6583.jpg

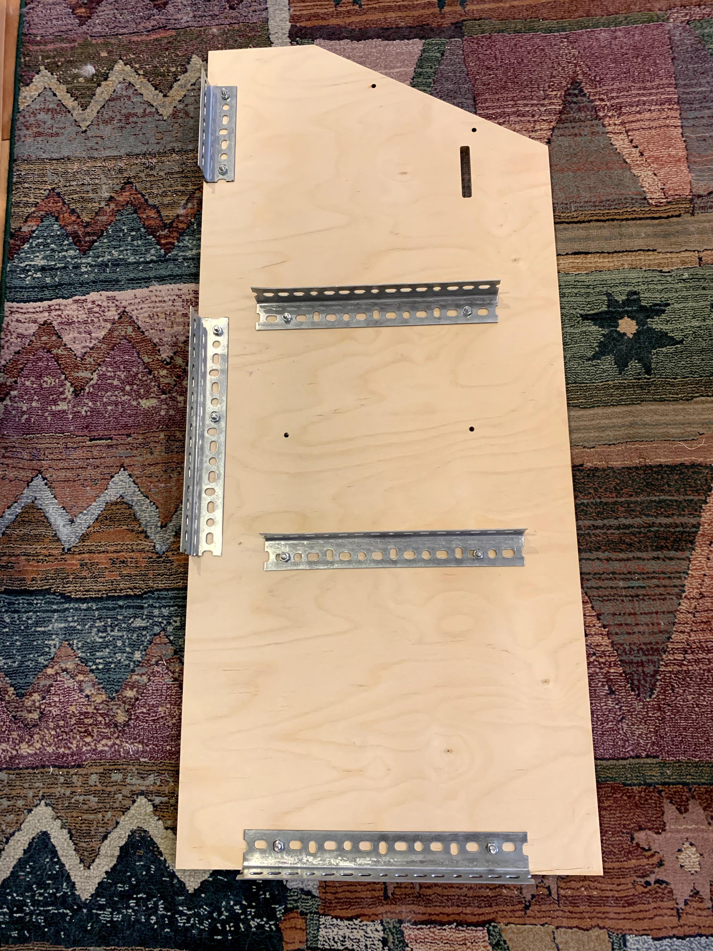
images/building_base/IMG_6583.jpg
