vizicist/spacepalettepro/images/building_base/IMG_6585.jpg

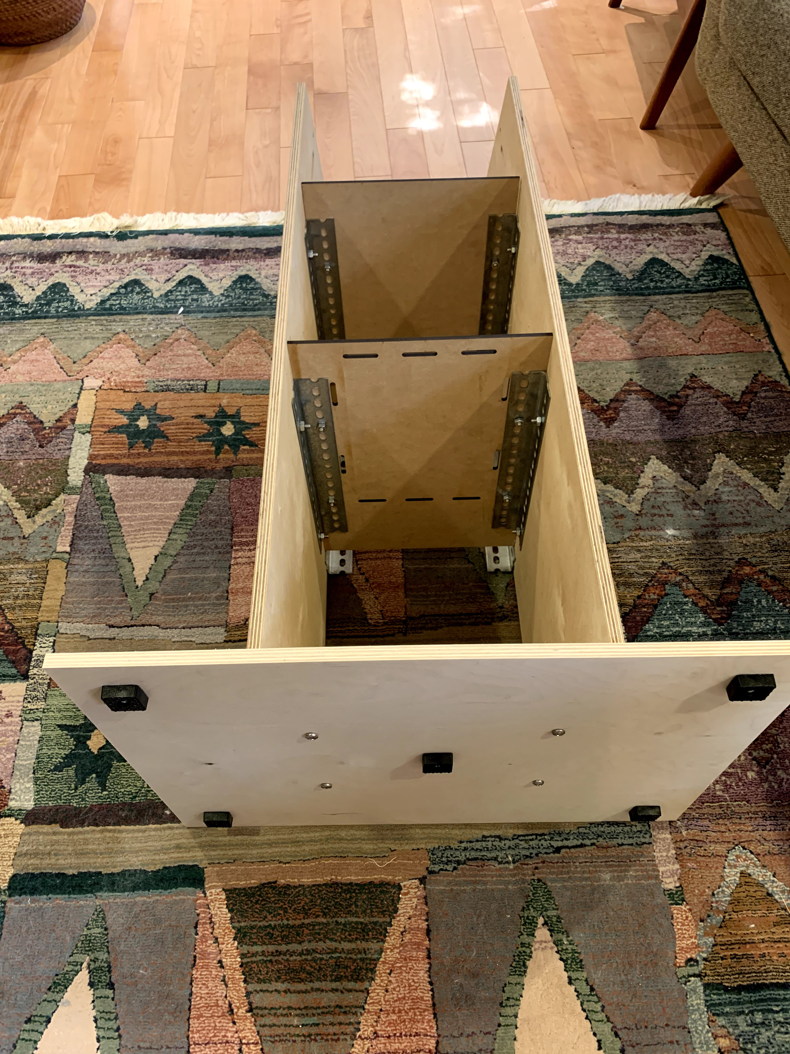
images/building_base/IMG_6585.jpg
