vizicist/spacepalettepro/images/building_base/IMG_6586.jpg

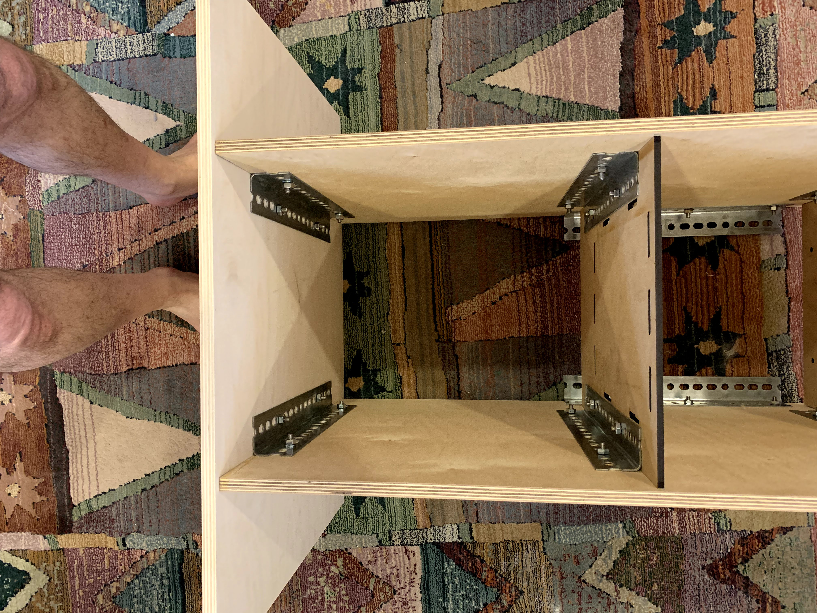
images/building_base/IMG_6586.jpg
