vizicist/spacepalettepro/images/building_base/IMG_6587.jpg

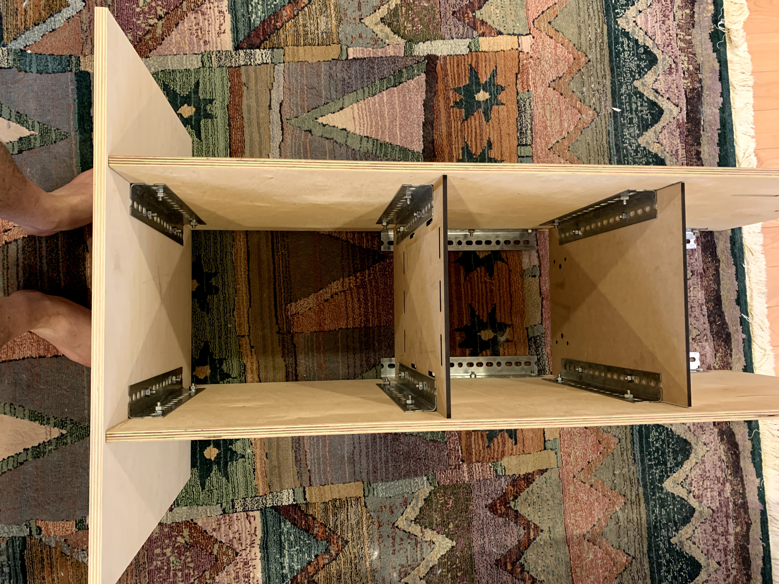
images/building_base/IMG_6587.jpg
