vizicist/spacepalettepro/images/building_controller/IMG_6275.jpg

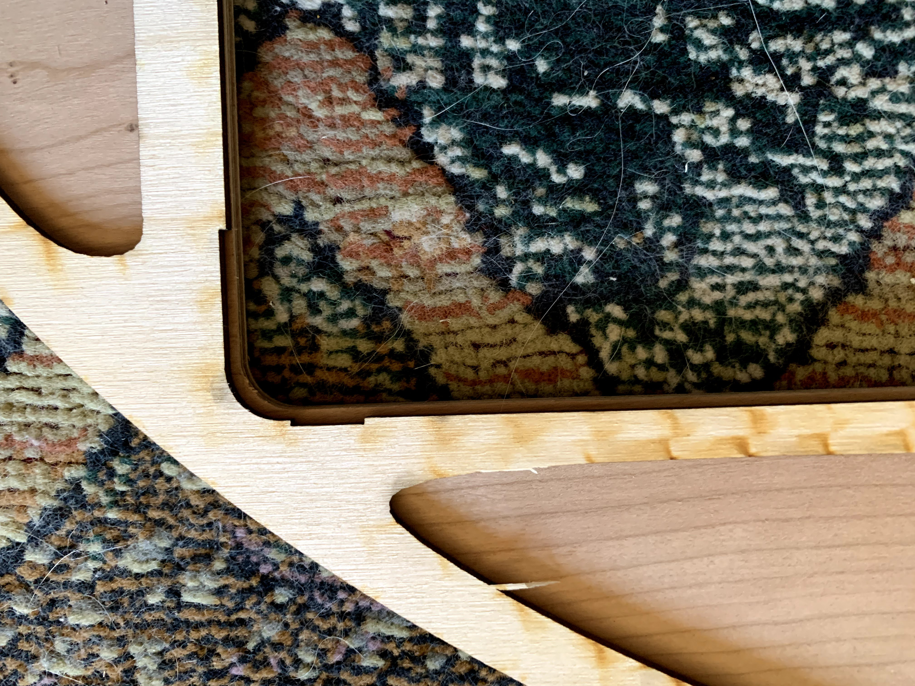
images/building_controller/IMG_6275.jpg
