vizicist/spacepalettepro/images/building_controller/IMG_6278.jpg

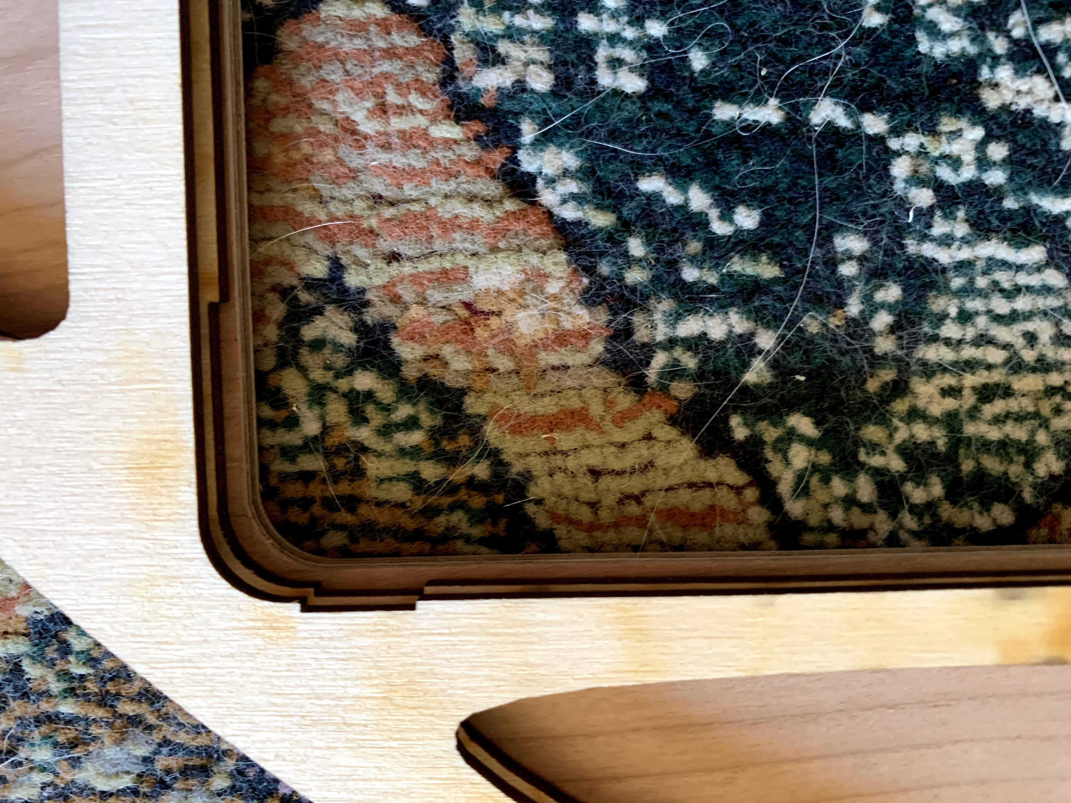
images/building_controller/IMG_6278.jpg
