vizicist/spacepalettepro/images/building_controller/IMG_6286.jpg

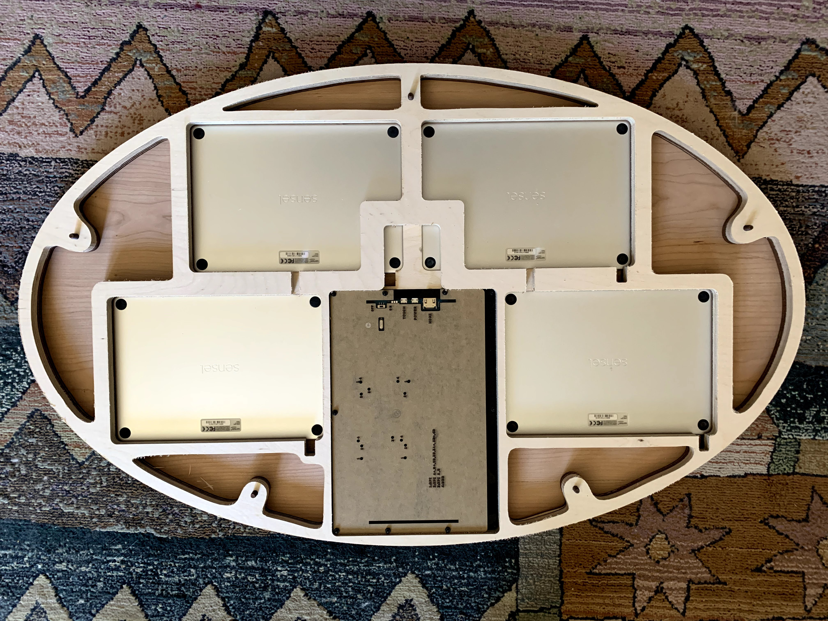
images/building_controller/IMG_6286.jpg
